angrychisel/makelab-chs-MCAPP/MORGAN/FAB APPROVED STL/STL OUTPUT SETTINGS.PNG

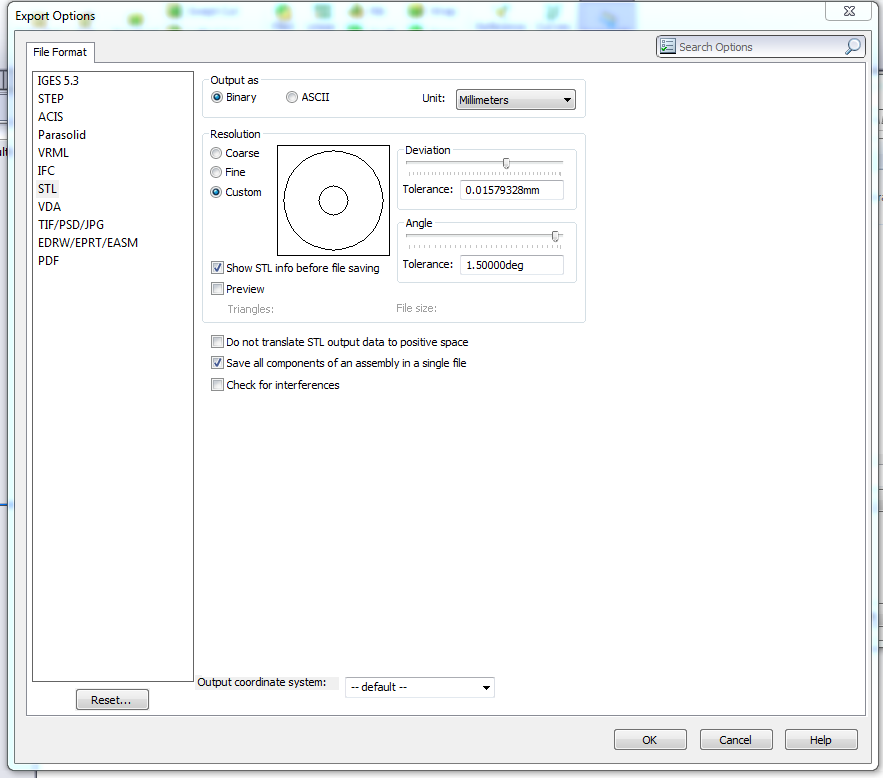
MORGAN/FAB APPROVED STL/STL OUTPUT SETTINGS.PNG
