angrychisel/makelab-chs-MCAPP/MORGAN/IMAGES/2013-07-30 22.37.16.jpg

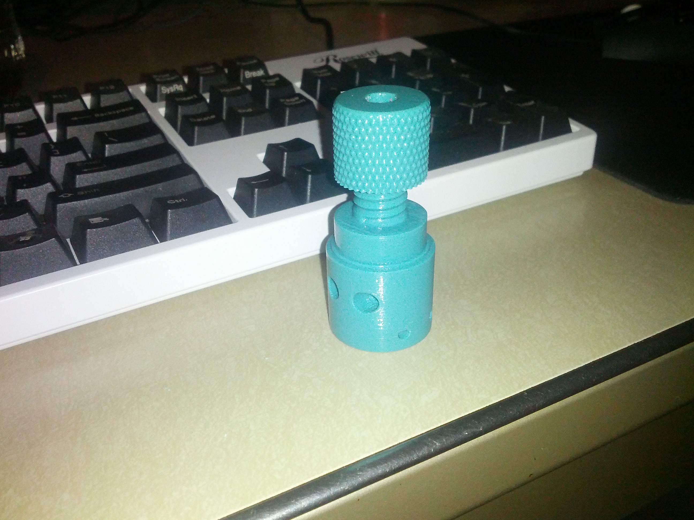
MORGAN/IMAGES/2013-07-30 22.37.16.jpg
