angrychisel/makelab-chs-MCAPP/MORGAN/IMAGES/2013-07-30 22.37.23.jpg

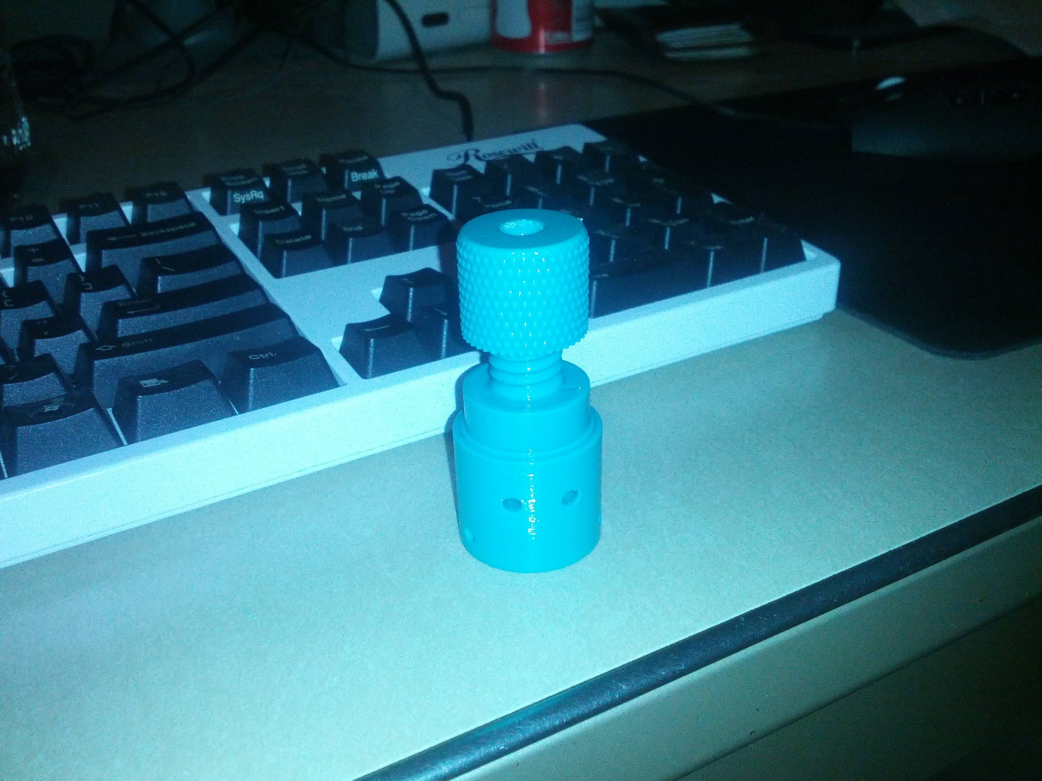
MORGAN/IMAGES/2013-07-30 22.37.23.jpg
