angrychisel/makelab-chs-MCAPP/MORGAN/IMAGES/2013-07-30 22.37.25.jpg

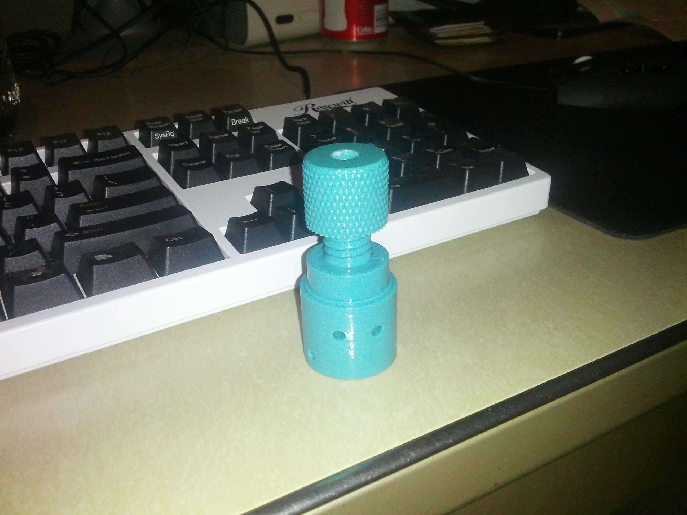
MORGAN/IMAGES/2013-07-30 22.37.25.jpg
