angrychisel/makelab-chs-MCAPP/MORGAN/IMAGES/2013-07-30 22.37.32.jpg

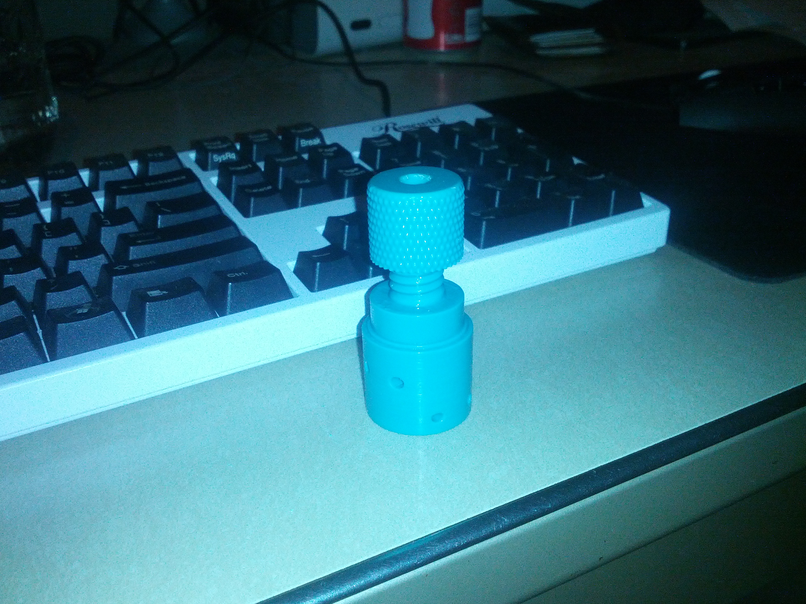
MORGAN/IMAGES/2013-07-30 22.37.32.jpg
