angrychisel/makelab-chs-MCAPP/MORGAN/IMAGES/2013-07-30 22.38.56.jpg

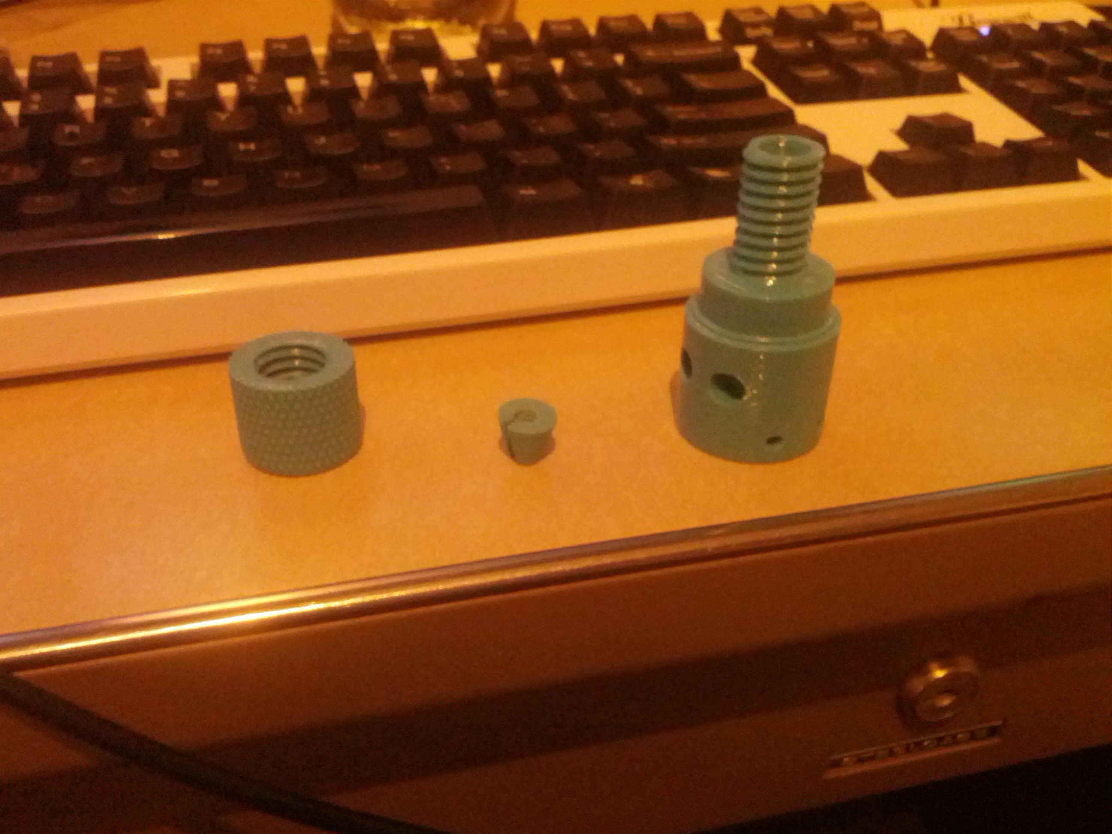
MORGAN/IMAGES/2013-07-30 22.38.56.jpg
