angrychisel/makelab-chs-MCAPP/MORGAN/IMAGES/2013-07-30 22.39.08.jpg

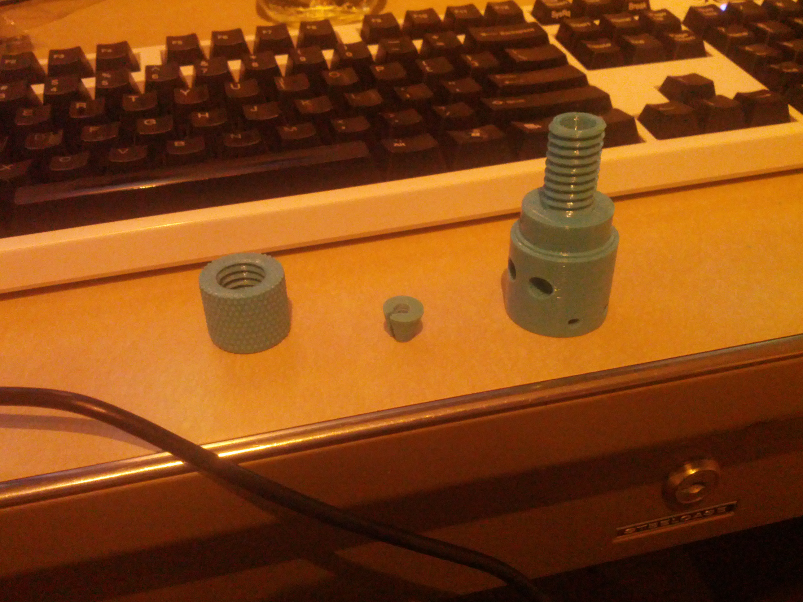
MORGAN/IMAGES/2013-07-30 22.39.08.jpg
