angrychisel/makelab-chs-MCAPP/MORGAN/IMAGES/2013-07-31 16.57.55.jpg

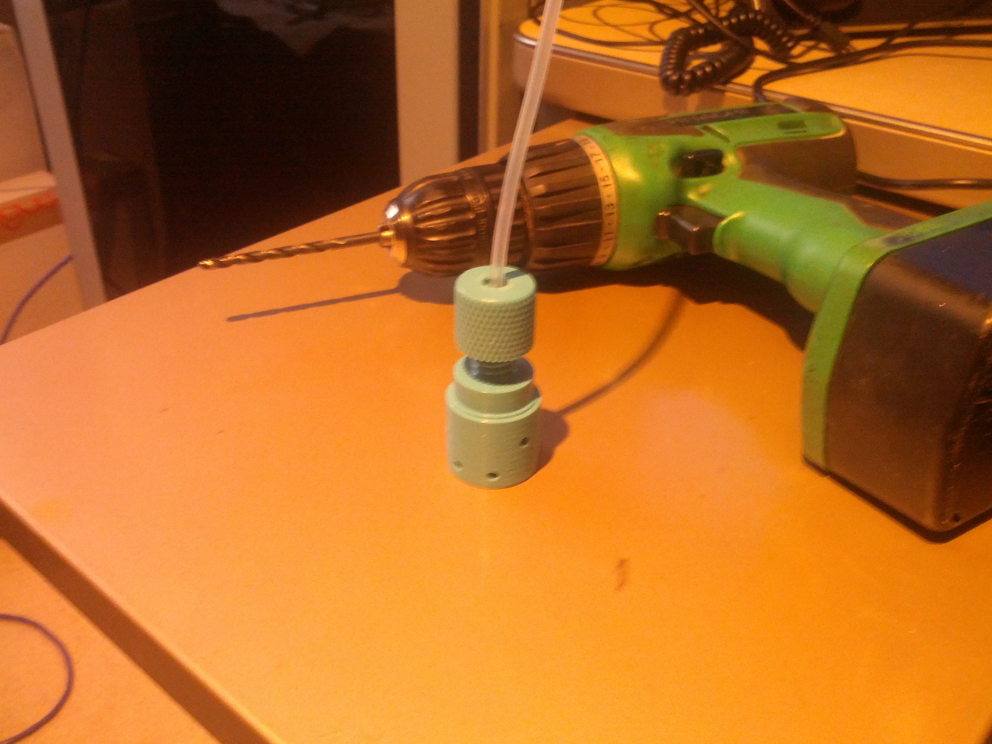
MORGAN/IMAGES/2013-07-31 16.57.55.jpg
