angrychisel/makelab-chs-MCAPP/MORGAN/IMAGES/2013-07-31 16.58.13.jpg

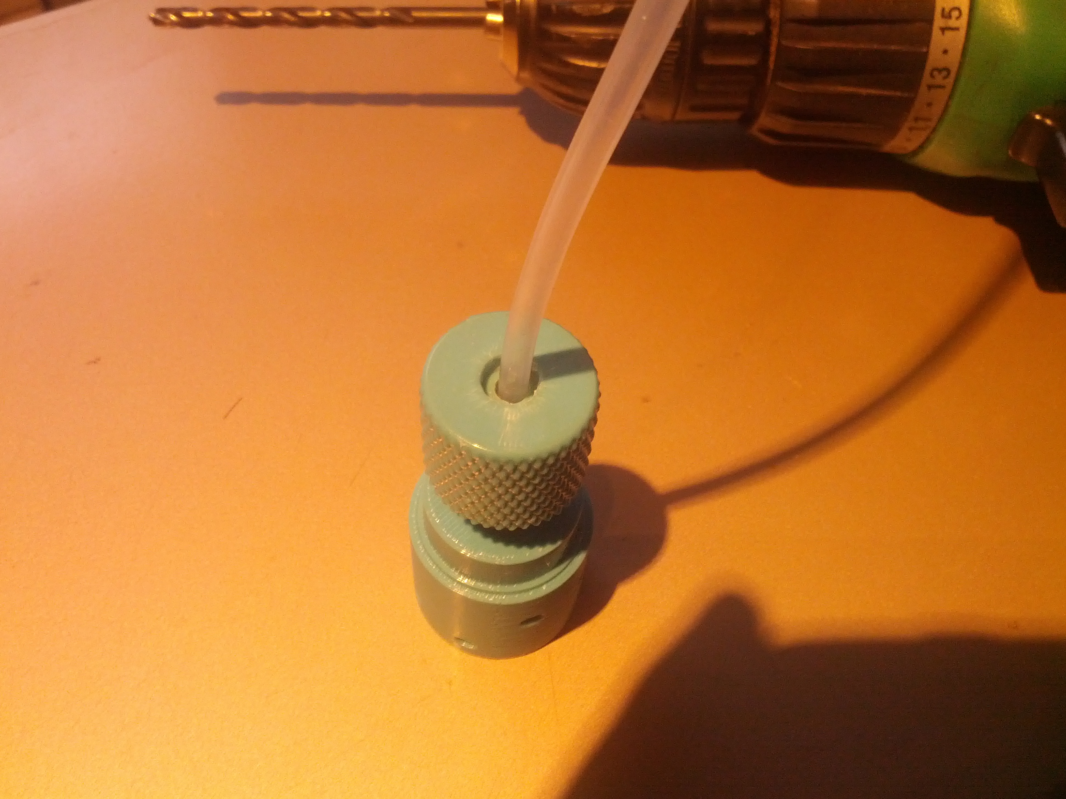
MORGAN/IMAGES/2013-07-31 16.58.13.jpg
