angrychisel/makelab-chs-MCAPP/MORGAN/IMAGES/2013-07-31 16.58.45.jpg

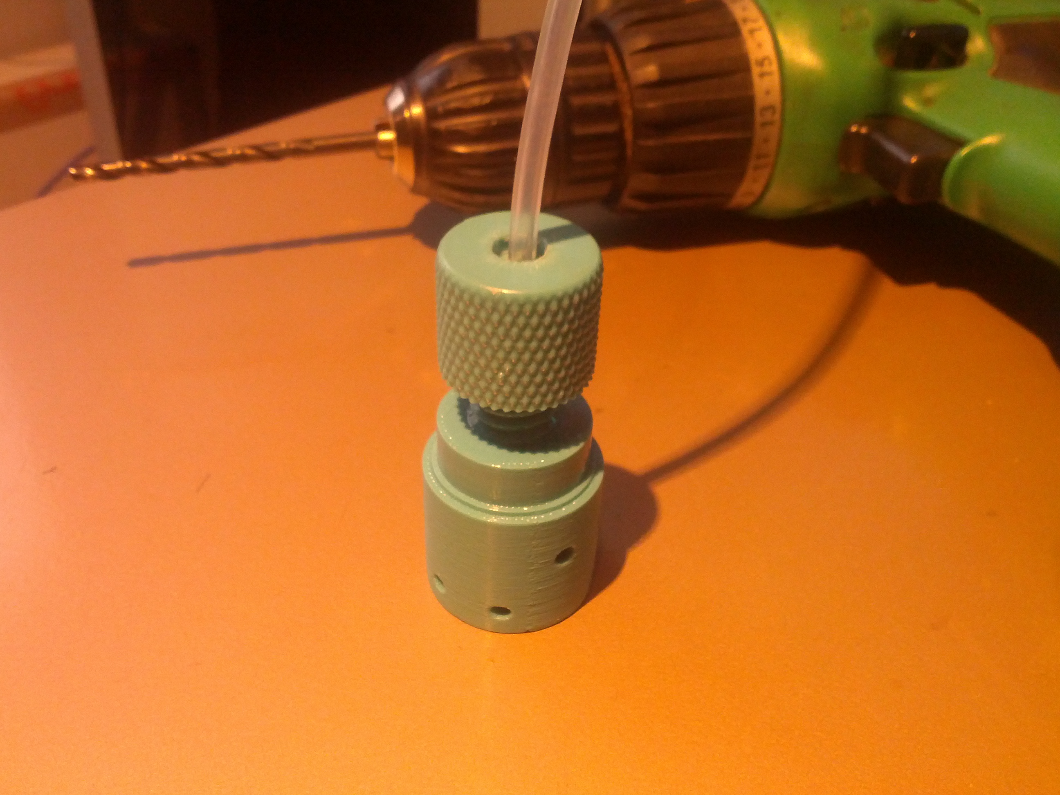
MORGAN/IMAGES/2013-07-31 16.58.45.jpg
