angrychisel/makelab-chs-MCAPP/MORGAN/IMAGES/2013-07-31 17.22.50.jpg

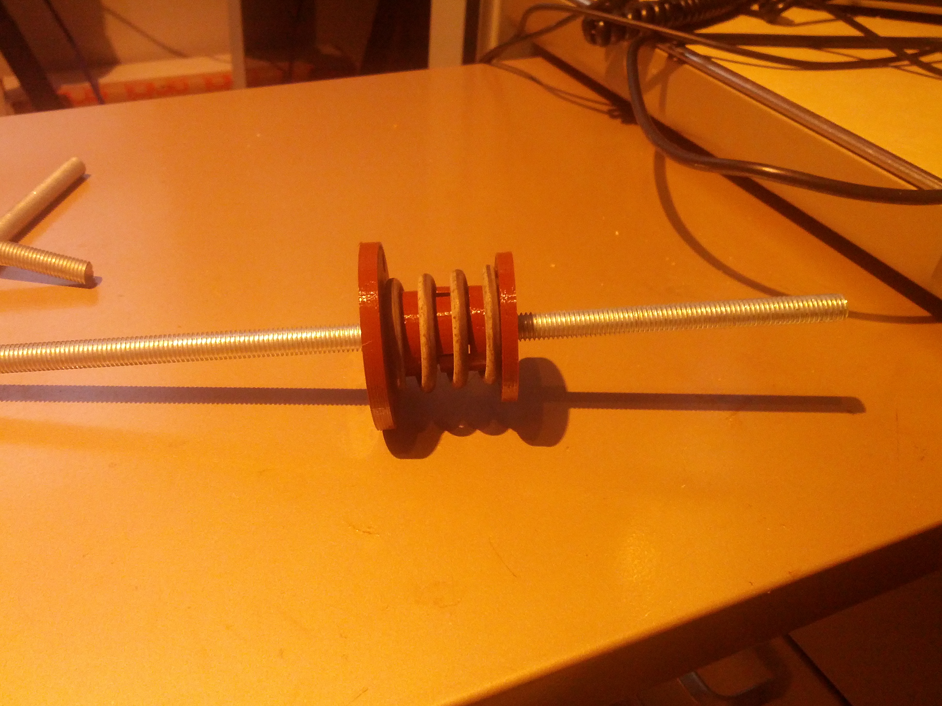
MORGAN/IMAGES/2013-07-31 17.22.50.jpg
