angrychisel/makelab-chs-MCAPP/MORGAN/IMAGES/2013-07-31 17.23.13.jpg

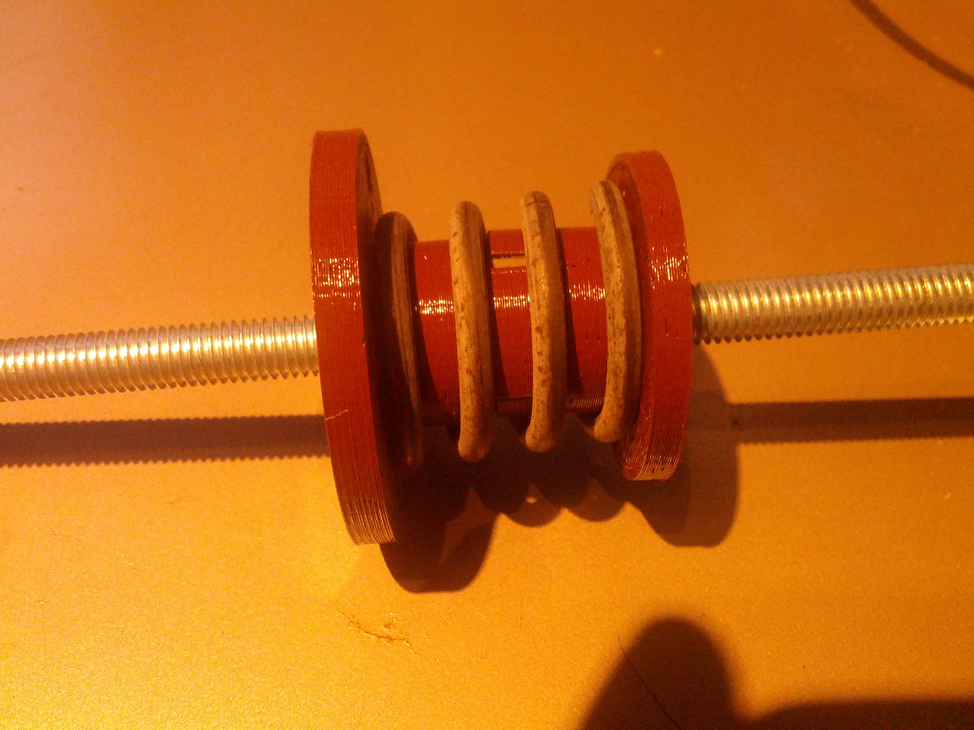
MORGAN/IMAGES/2013-07-31 17.23.13.jpg
