angrychisel/makelab-chs-MCAPP/MORGAN/IMAGES/2013-08-02 20.06.50.jpg

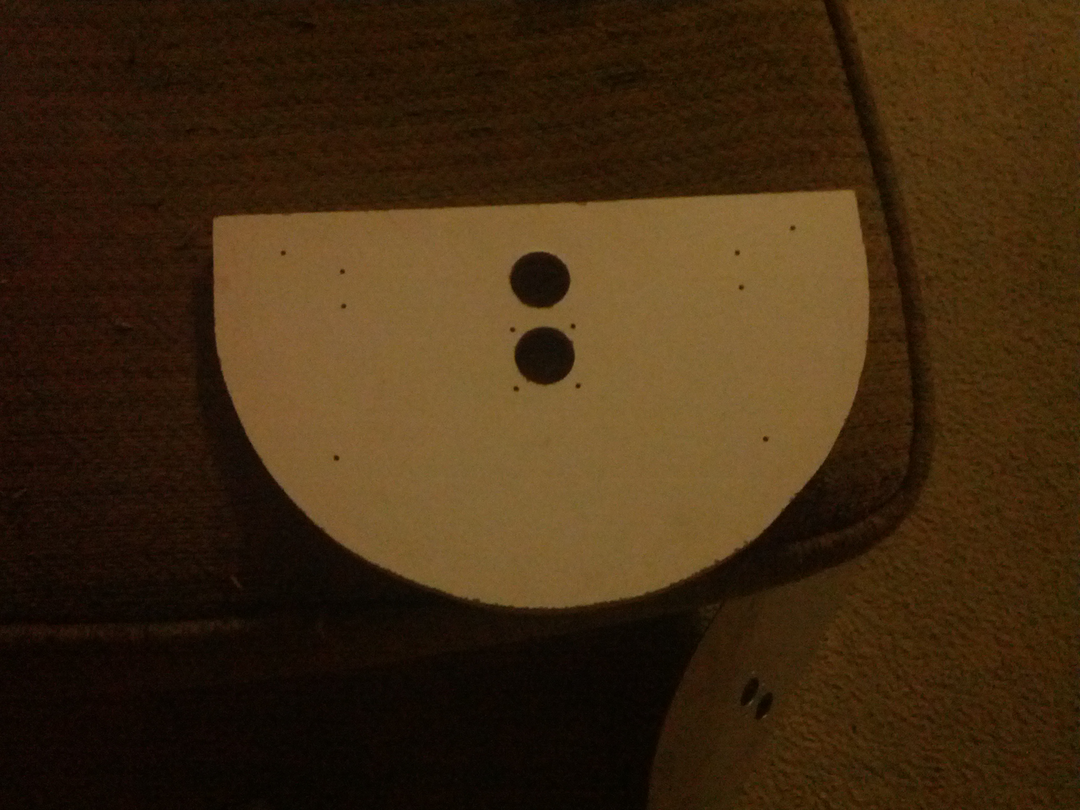
MORGAN/IMAGES/2013-08-02 20.06.50.jpg
