angrychisel/makelab-chs-MCAPP/MORGAN/IMAGES/2013-08-02 20.07.16.jpg

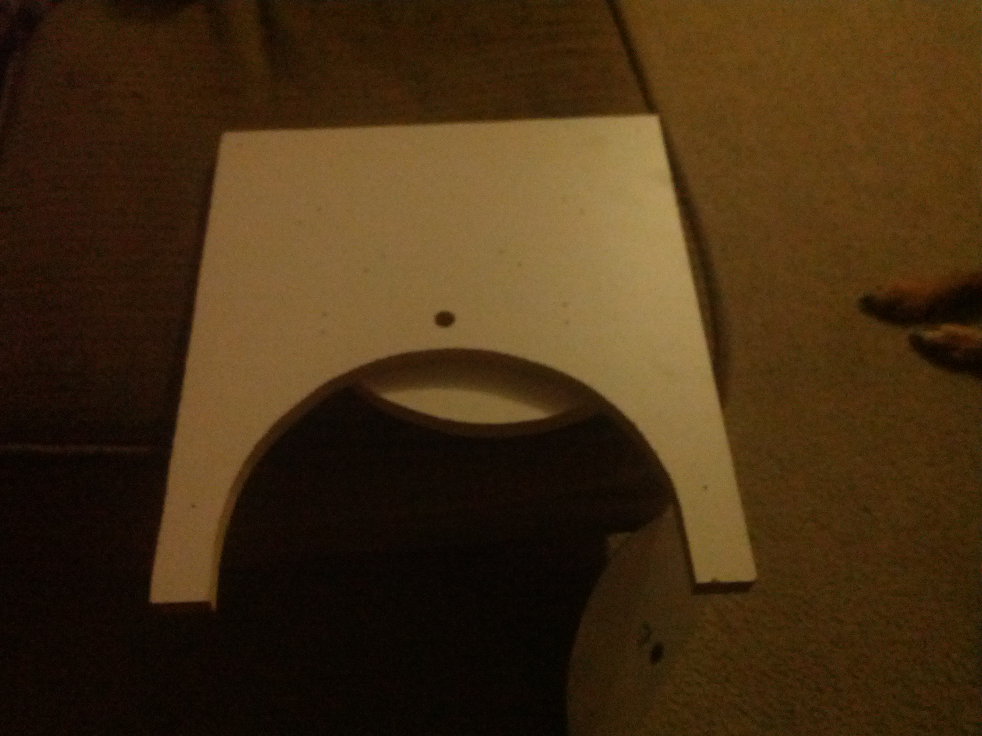
MORGAN/IMAGES/2013-08-02 20.07.16.jpg
