angrychisel/makelab-chs-MCAPP/MORGAN/IMAGES/2013-08-03 15.07.32.jpg

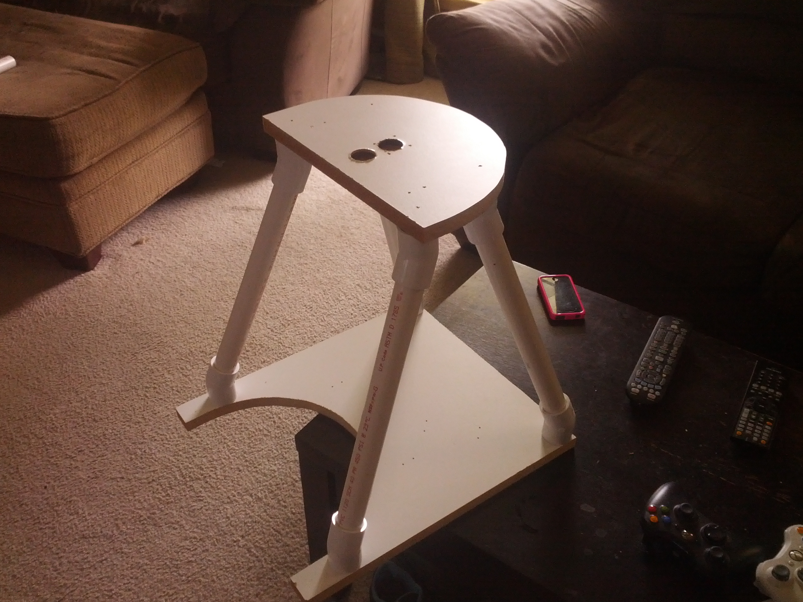
MORGAN/IMAGES/2013-08-03 15.07.32.jpg
