angrychisel/makelab-chs-MCAPP/MORGAN/IMAGES/image005.jpg

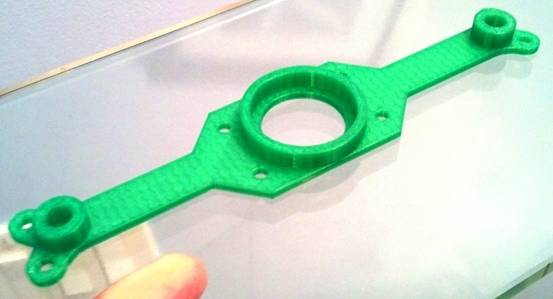
MORGAN/IMAGES/image005.jpg
