angrychisel/makelab-chs-MCAPP/MORGAN/IMAGES/image006.jpg

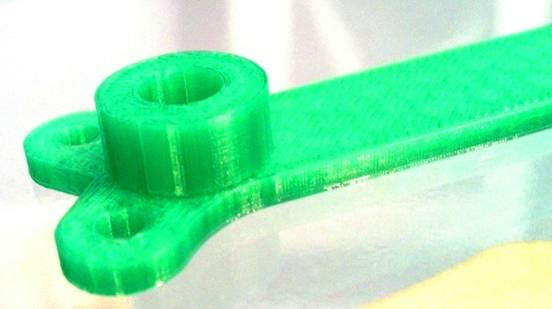
MORGAN/IMAGES/image006.jpg
