angrychisel/makelab-chs-MCAPP/MORGAN/Morgan-master/MorganHarley1.jpg

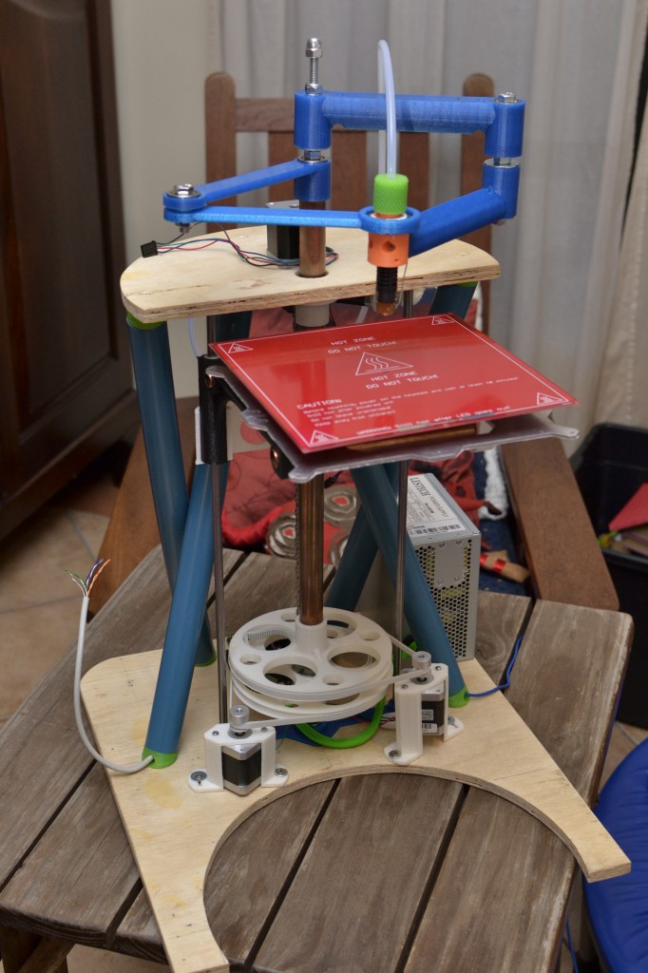
MORGAN/Morgan-master/MorganHarley1.jpg
