angrychisel/makelab-chs-MCAPP/MORGAN/FAB APPROVED STL/MLC-1-0029.STL

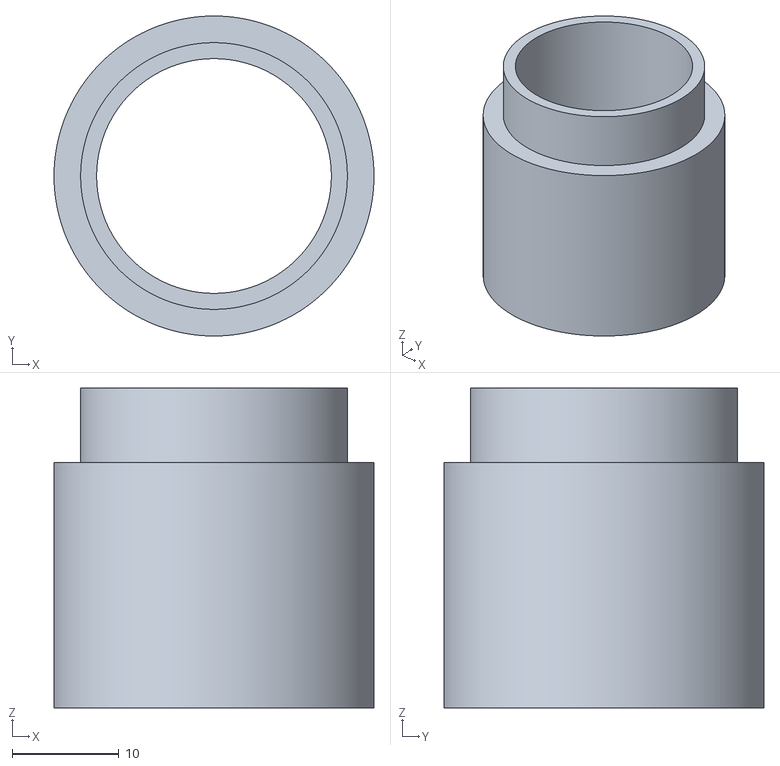
[picture p51: CAD file, 2013-08-08]
MORGAN/FAB APPROVED STL/MLC-1-0029.STL
30.0 x 30.0 x 30.0
