angrychisel/makelab-chs-MCAPP/MORGAN/Morgan-master/dxf/UNIVERSAL PLATE.SLDPRT

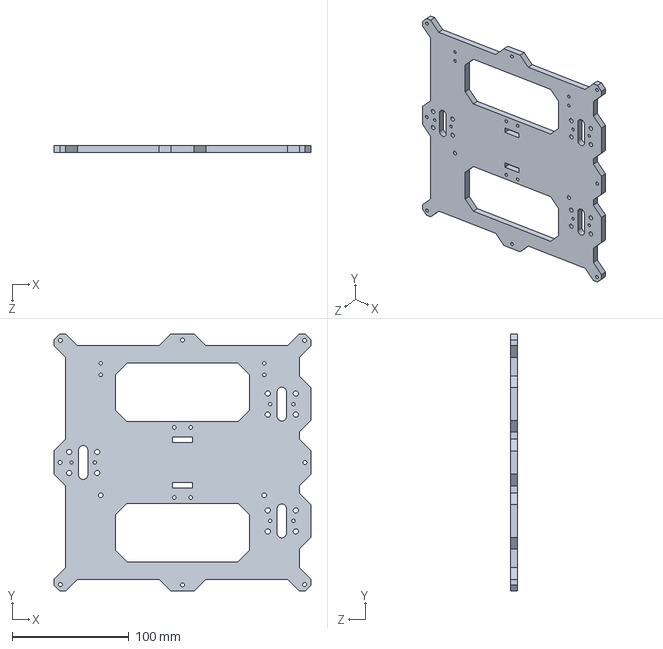
[picture p52: CAD file, 2013-07-29]
MORGAN/Morgan-master/dxf/UNIVERSAL PLATE.SLDPRT
220.0 x 220.0 x 6.35 mm
