angrychisel/makelab-chs-MCAPP/MORGAN/Morgan-master/source/Base_and_Riser_2.stl

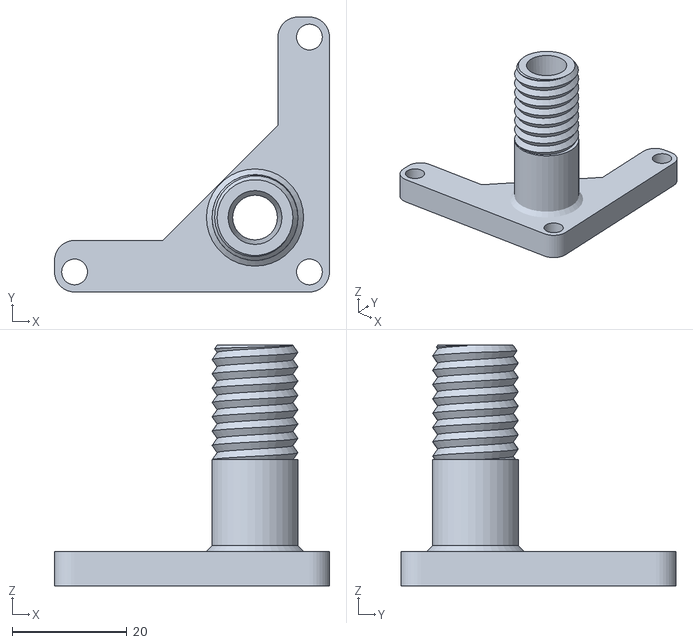
[picture p53: CAD file, 2013-07-25]
MORGAN/Morgan-master/source/Base_and_Riser_2.stl
48.0 x 48.0 x 42.0
