angrychisel/makelab-chs-MCAPP/MORGAN/Morgan-master/stl/NEMA17STEPPER.SLDPRT

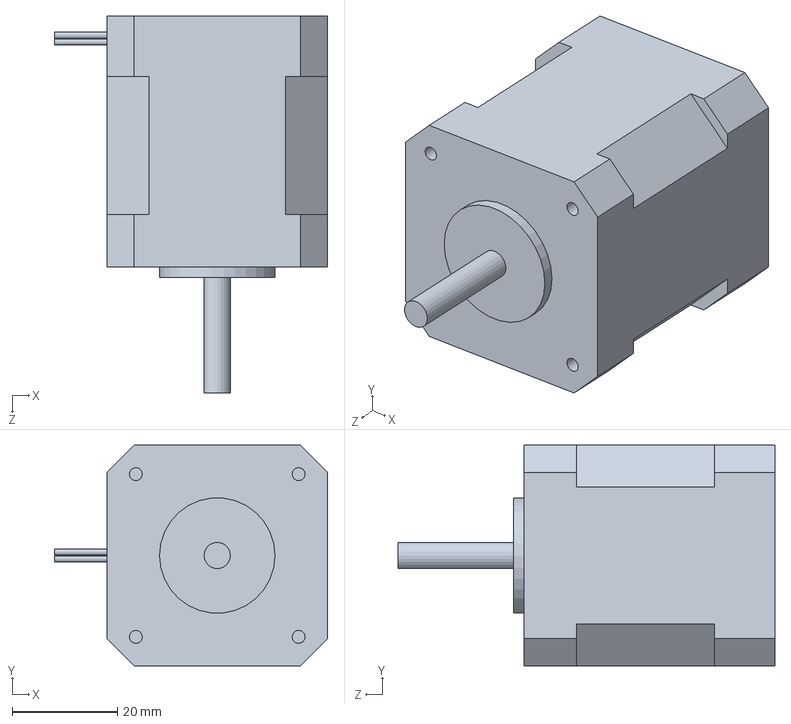
[picture p54: CAD file, 2013-07-26]
MORGAN/Morgan-master/stl/NEMA17STEPPER.SLDPRT
52.0 x 42.0 x 71.8 mm
