angrychisel/makelab-chs-MCAPP/MORGAN/WORM EXTRUDER/g1034.SLDPRT

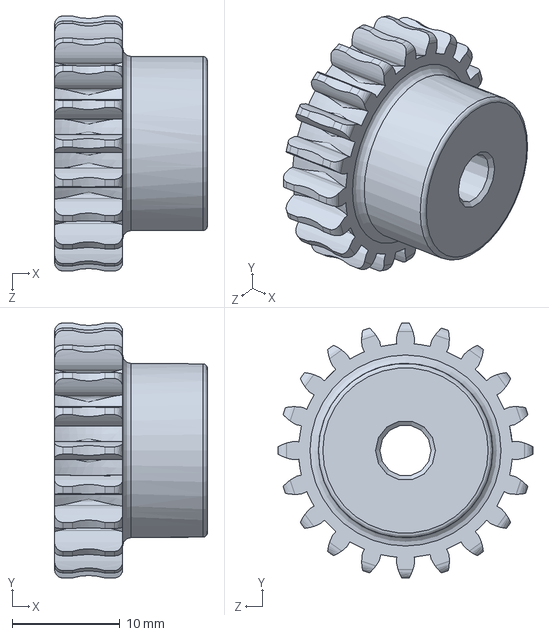
[picture p55: CAD file, 2013-07-27]
MORGAN/WORM EXTRUDER/g1034.SLDPRT
14.2 x 23.7 x 23.7 mm
