angrychisel/makelab-chs-MCAPP/MORGAN/ACCESSORIES/SPOOL ROLLER.SLDPRT

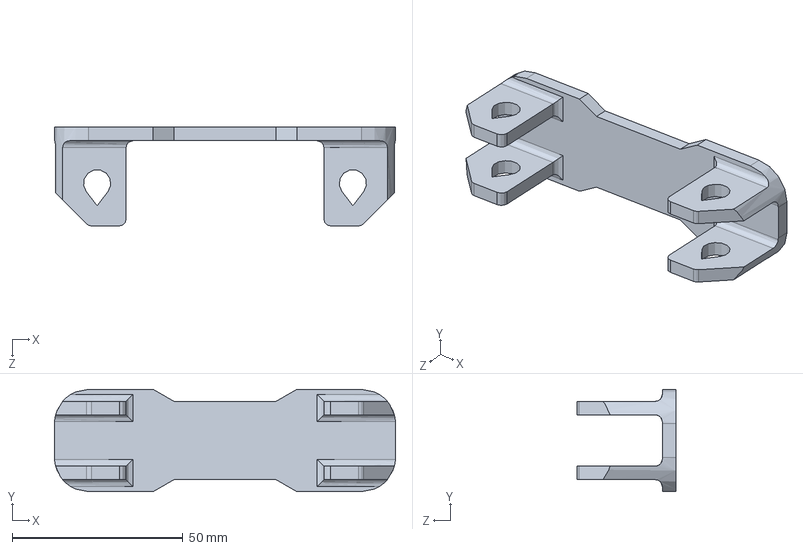
[picture p56: CAD file, 2013-10-28]
MORGAN/ACCESSORIES/SPOOL ROLLER.SLDPRT
100.0 x 30.0 x 29.0 mm
