angrychisel/makelab-chs-MCAPP/MORGAN/FAB APPROVED STL/MLC-1-0019.STL

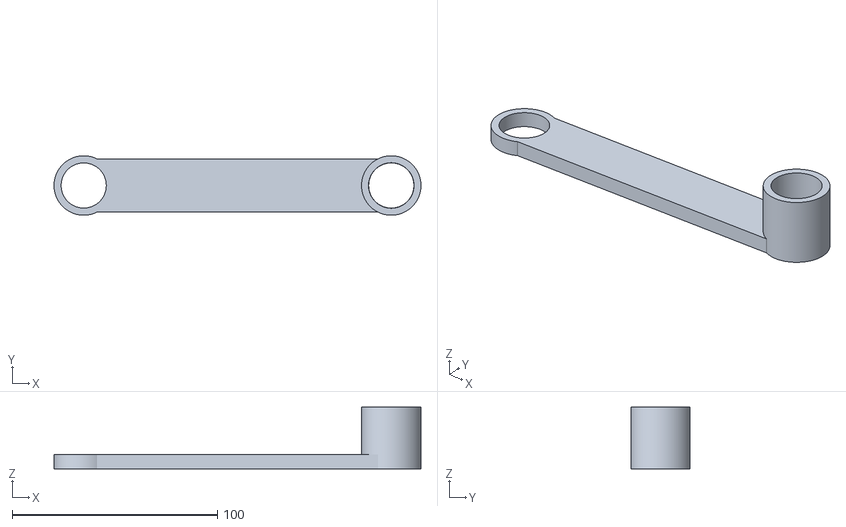
[picture p57: CAD file, 2013-08-04]
MORGAN/FAB APPROVED STL/MLC-1-0019.STL
179.0 x 29.0 x 30.0
