angrychisel/makelab-chs-MCAPP/MORGAN/good extruder/h3216.SLDPRT

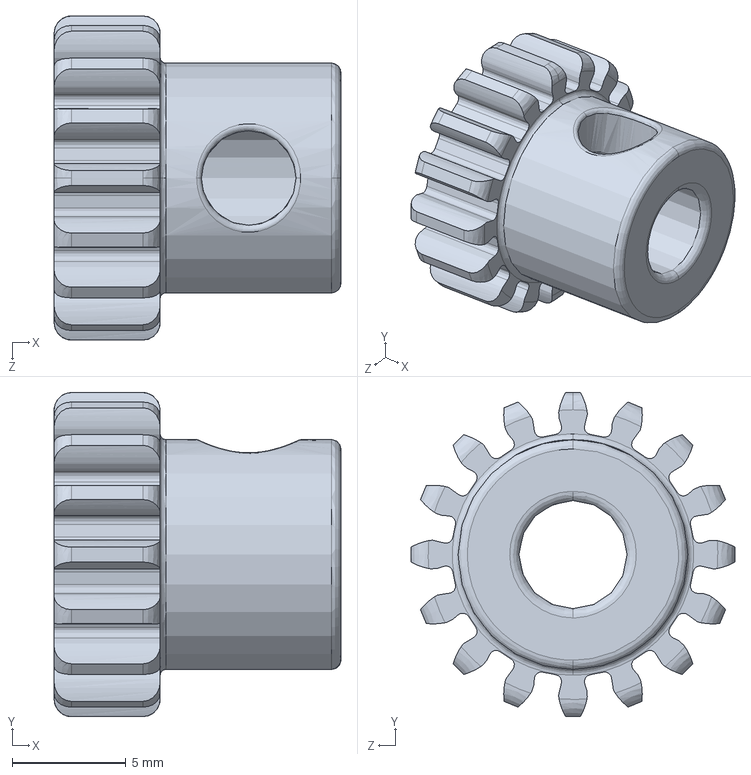
[picture p58: CAD file, 2013-09-19]
MORGAN/good extruder/h3216.SLDPRT
12.6 x 14.3 x 14.3 mm
