angrychisel/makelab-chs-MCAPP/MORGAN/MLC-1-0017.SLDPRT

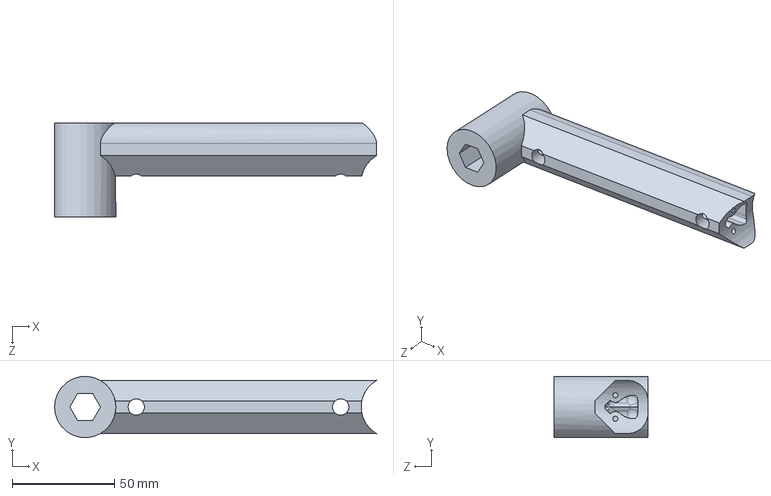
[picture p59: CAD file, 2013-10-12]
MORGAN/MLC-1-0017.SLDPRT
157.5 x 29.9 x 46.0 mm
