angrychisel/makelab-chs-MCAPP/MORGAN/Morgan-master/dxf/OpenHW_Universal-XPlate.dxf

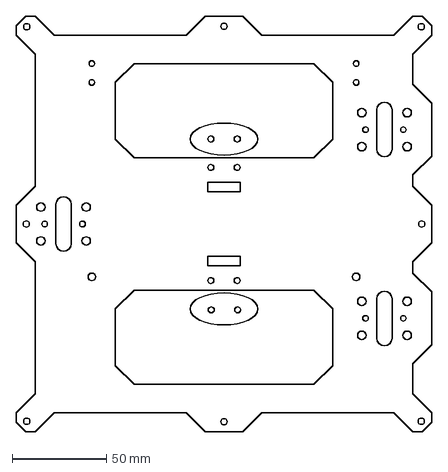
[picture p60: CAD file, 2013-07-25]
MORGAN/Morgan-master/dxf/OpenHW_Universal-XPlate.dxf
220.0 x 220.0 mm
