angrychisel/makelab-chs-MCAPP/MORGAN/Morgan-master/stl/19-Morgan_arm_Theta_a.stl

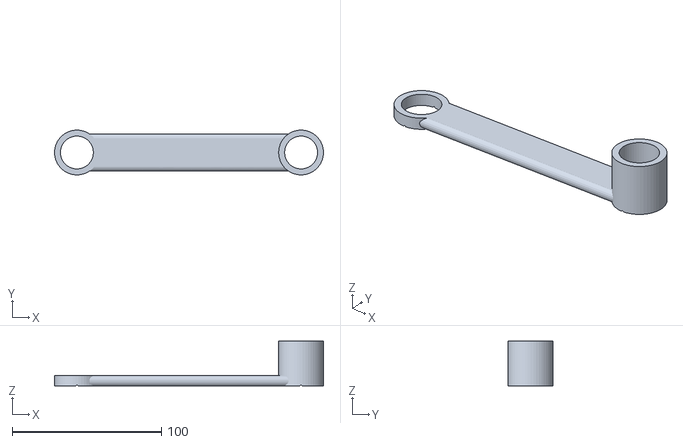
[picture p61: CAD file, 2013-07-25]
MORGAN/Morgan-master/stl/19-Morgan_arm_Theta_a.stl
180.0 x 29.9 x 30.0
