angrychisel/makelab-chs-MCAPP/MORGAN/WORM EXTRUDER/g1035.SLDPRT

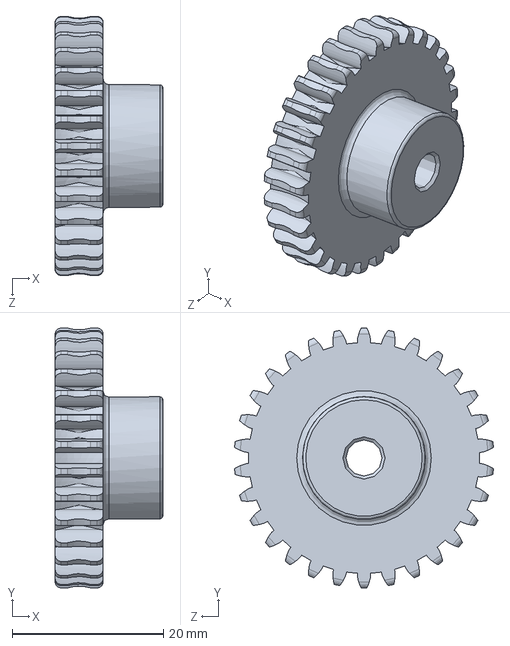
[picture p62: CAD file, 2013-07-27]
MORGAN/WORM EXTRUDER/g1035.SLDPRT
14.2 x 34.3 x 34.2 mm
