angrychisel/makelab-chs-MCAPP/MORGAN/EXPERIMENTAL/testcube.SLDPRT

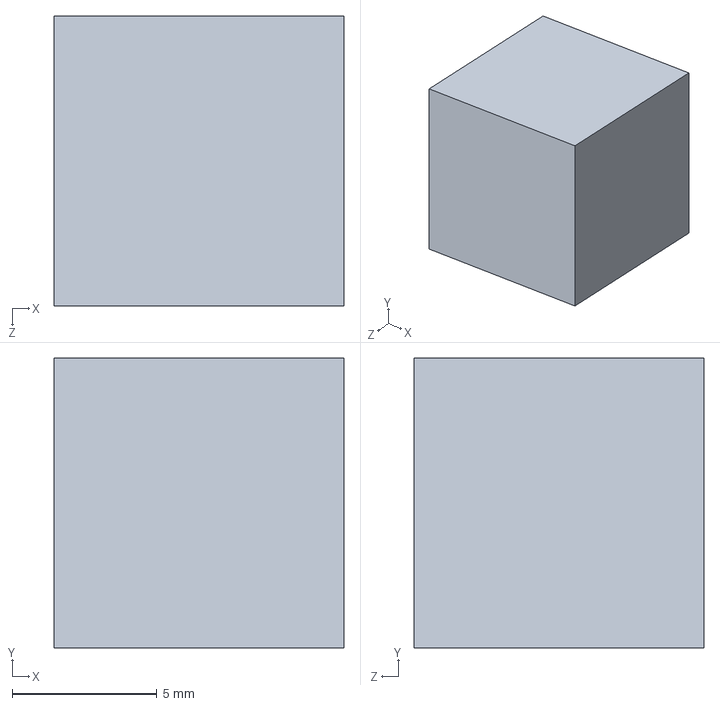
[picture p63: CAD file, 2013-09-19]
MORGAN/EXPERIMENTAL/testcube.SLDPRT
10.0 x 10.0 x 10.0 mm
