angrychisel/makelab-chs-MCAPP/MORGAN/FAB APPROVED STL/MLC-1-002.DXF

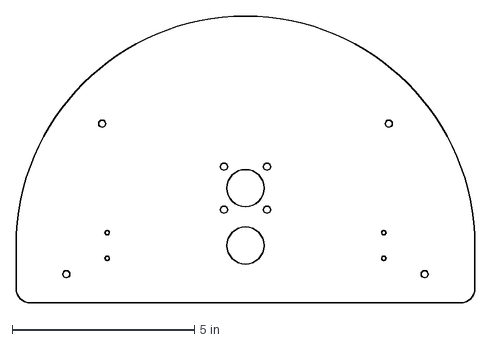
[picture p64: CAD file, 2013-08-02]
MORGAN/FAB APPROVED STL/MLC-1-002.DXF
12.6 x 7.87 in
