angrychisel/makelab-chs-MCAPP/MORGAN/good extruder/spur gear_ai.sldprt

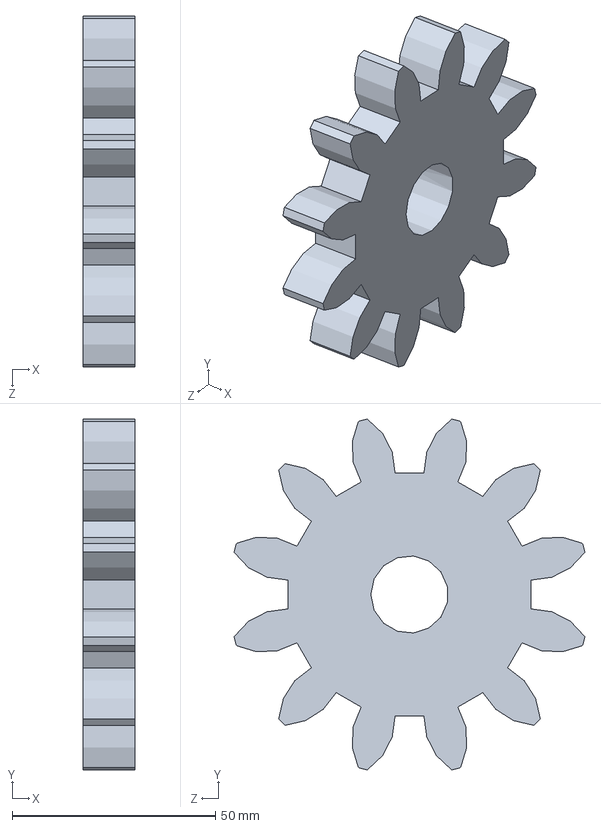
[picture p65: CAD file, 2013-09-19]
MORGAN/good extruder/spur gear_ai.sldprt
12.7 x 86.4 x 86.4 mm
