angrychisel/makelab-chs-MCAPP/MORGAN/Morgan-master/dxf/platform_cutting.dxf

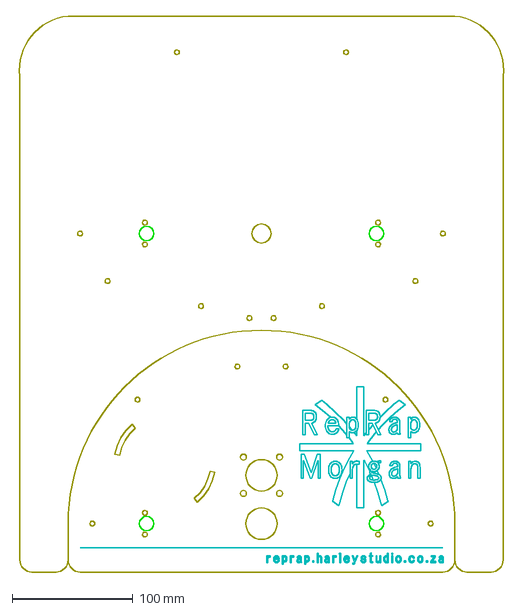
[picture p66: CAD file, 2013-07-25]
MORGAN/Morgan-master/dxf/platform_cutting.dxf
405.5 x 460.0 mm
