angrychisel/makelab-chs-MCAPP/MORGAN/Morgan-master/stl/01-pvc_pipe_support_a.SLDPRT

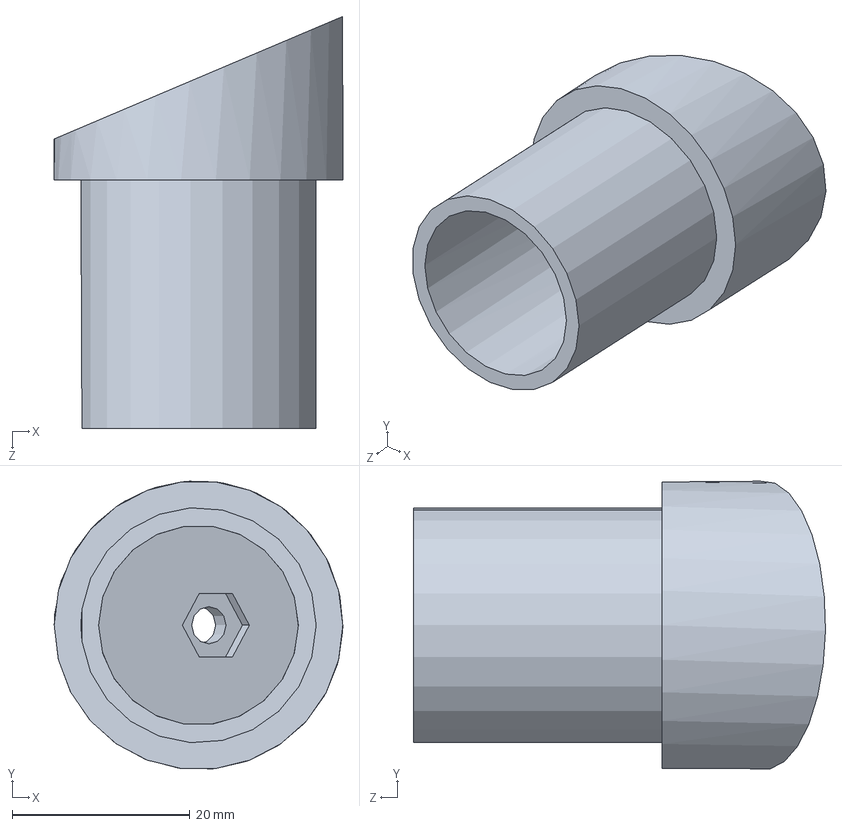
[picture p67: CAD file, 2013-07-25]
MORGAN/Morgan-master/stl/01-pvc_pipe_support_a.SLDPRT
32.5 x 32.4 x 46.4 mm
