angrychisel/makelab-chs-MCAPP/MORGAN/WORM EXTRUDER/LUHB.SLDPRT

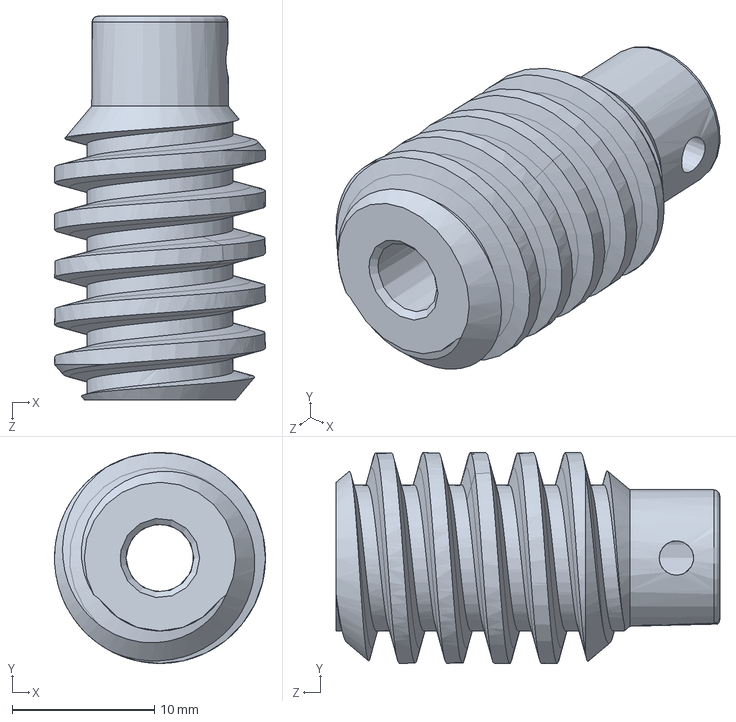
[picture p68: CAD file, 2013-07-27]
MORGAN/WORM EXTRUDER/LUHB.SLDPRT
14.8 x 14.8 x 26.9 mm
