angrychisel/makelab-chs-MCAPP/MORGAN/EXPERIMENTAL/HEATBED BASE PLATE.SLDPRT

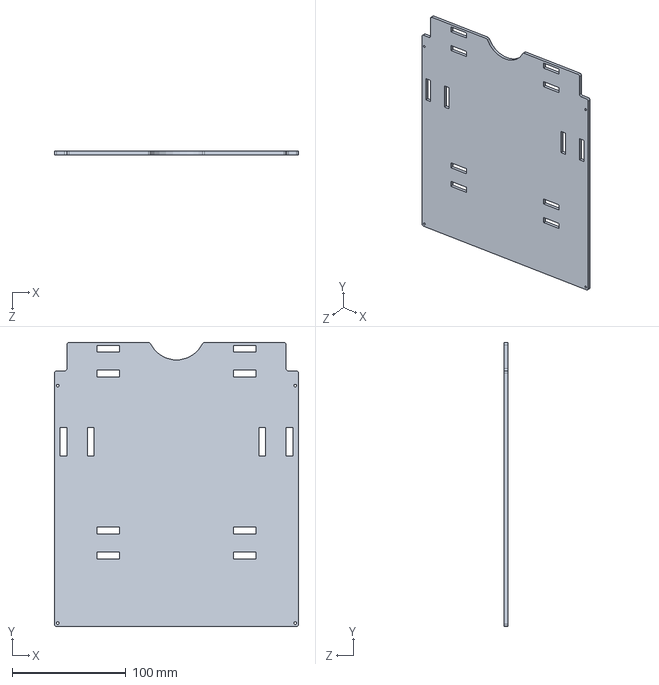
[picture p69: CAD file, 2013-09-14]
MORGAN/EXPERIMENTAL/HEATBED BASE PLATE.SLDPRT
215.0 x 250.0 x 3.17 mm
