angrychisel/makelab-chs-MCAPP/MORGAN/FAB APPROVED STL/MLC-1-001.DXF

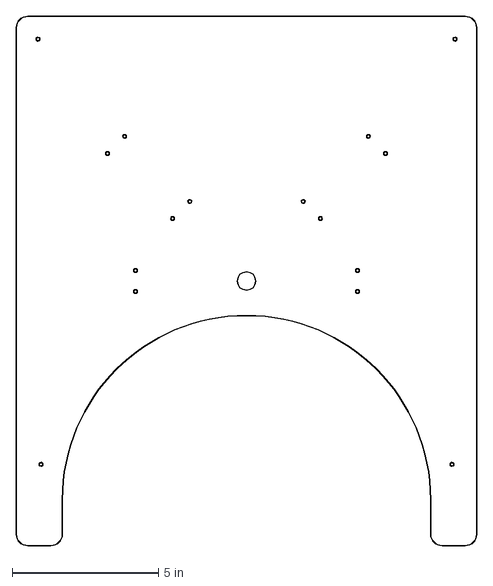
[picture p70: CAD file, 2013-08-02]
MORGAN/FAB APPROVED STL/MLC-1-001.DXF
15.7 x 18.1 in
