angrychisel/makelab-chs-MCAPP/MORGAN/MK2A Heatbed.SLDPRT

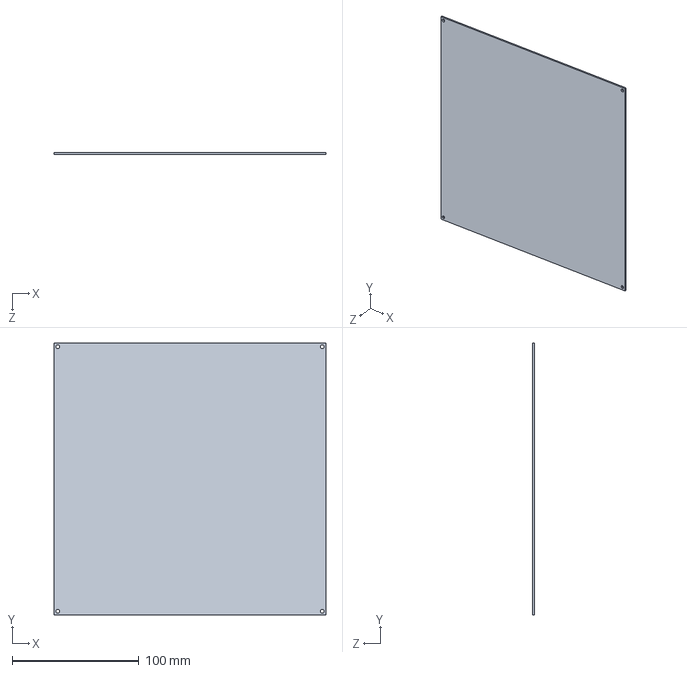
[picture p71: CAD file, 2013-09-10]
MORGAN/MK2A Heatbed.SLDPRT
215.0 x 215.0 x 1.60 mm
