angrychisel/makelab-chs-MCAPP/MORGAN/Morgan-master/stl/cap_2.stl

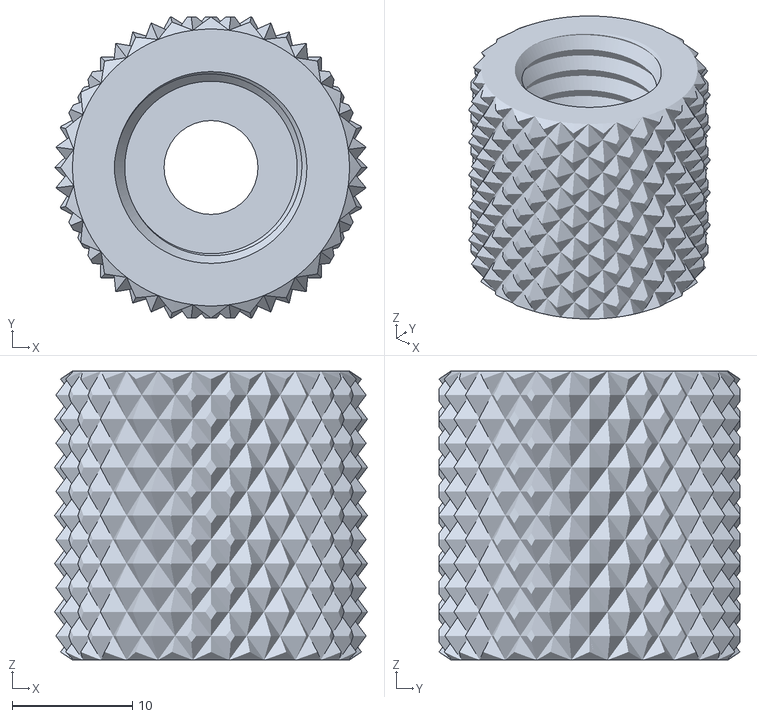
[picture p72: CAD file, 2013-07-25]
MORGAN/Morgan-master/stl/cap_2.stl
26.0 x 25.0 x 24.0
