angrychisel/makelab-chs-MCAPP/MORGAN/WORM EXTRUDER/STEPPER BASE.SLDPRT

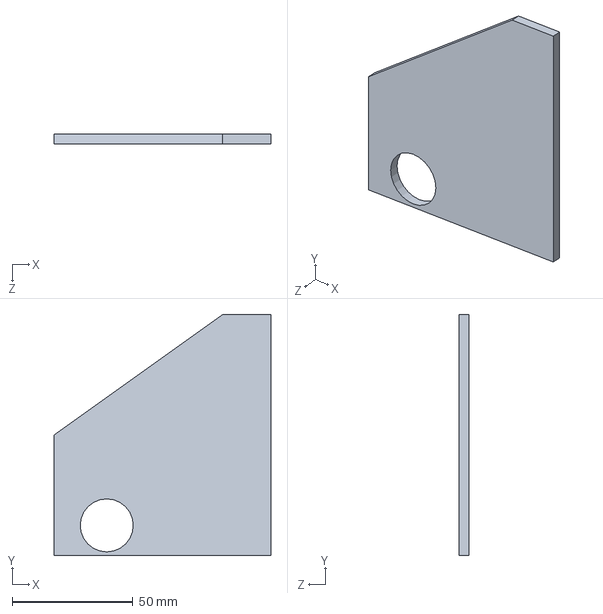
[picture p73: CAD file, 2013-07-27]
MORGAN/WORM EXTRUDER/STEPPER BASE.SLDPRT
90.0 x 100.0 x 4.00 mm
