angrychisel/makelab-chs-MCAPP/MORGAN/FAB APPROVED STL/MLC-1-0020.STL

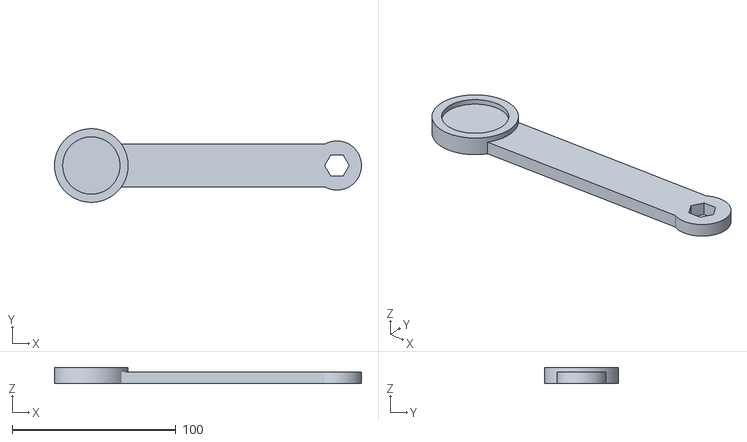
[picture p74: CAD file, 2013-08-01]
MORGAN/FAB APPROVED STL/MLC-1-0020.STL
187.5 x 45.0 x 10.00
