angrychisel/makelab-chs-MCAPP/MORGAN/MLC-1-009.SLDPRT

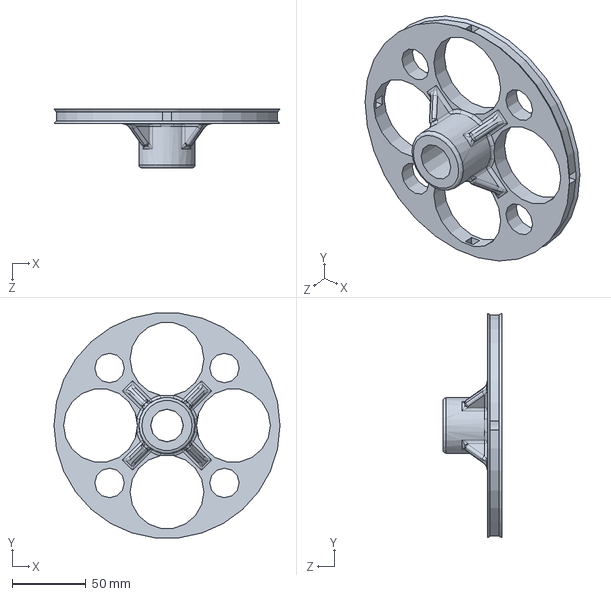
[picture p75: CAD file, 2013-08-04]
MORGAN/MLC-1-009.SLDPRT
153.0 x 152.2 x 40.0 mm
