angrychisel/makelab-chs-MCAPP/MORGAN/Morgan-master/stl/04-z_mount_top_8mm.stl

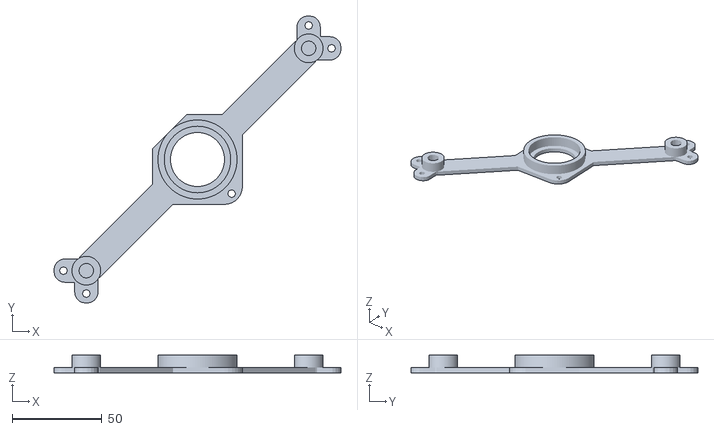
[picture p76: CAD file, 2013-07-25]
MORGAN/Morgan-master/stl/04-z_mount_top_8mm.stl
159.7 x 159.7 x 10.0
