angrychisel/makelab-chs-MCAPP/MORGAN/EXPERIMENTAL/airtripper-extruder-v3.SLDPRT

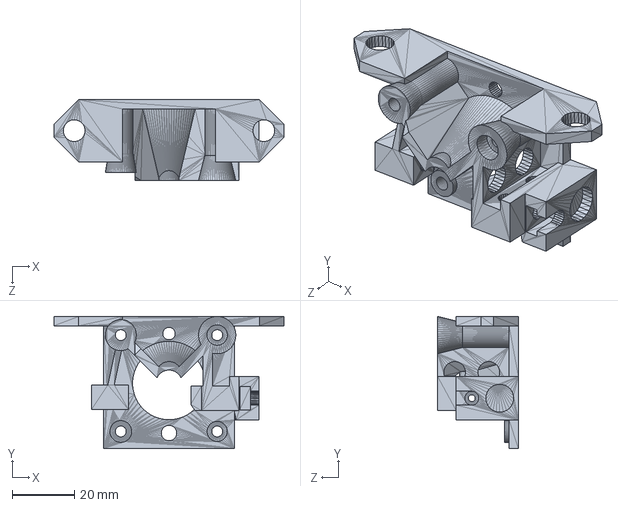
[picture p77: CAD file, 2013-09-13]
MORGAN/EXPERIMENTAL/airtripper-extruder-v3.SLDPRT
74.0 x 42.5 x 26.0 mm
