angrychisel/makelab-chs-MCAPP/MORGAN/FAB APPROVED STL/MLCE-1-002.STL

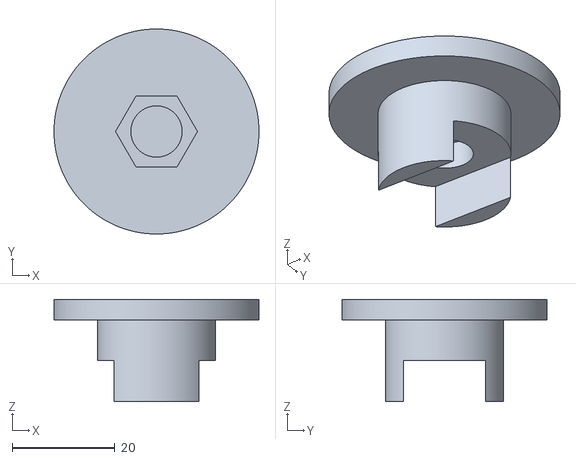
[picture p78: CAD file, 2013-07-30]
MORGAN/FAB APPROVED STL/MLCE-1-002.STL
40.0 x 40.0 x 20.0
