angrychisel/makelab-chs-MCAPP/MORGAN/Morgan-master/stl/23-extruder_bowden_adaptor.stl

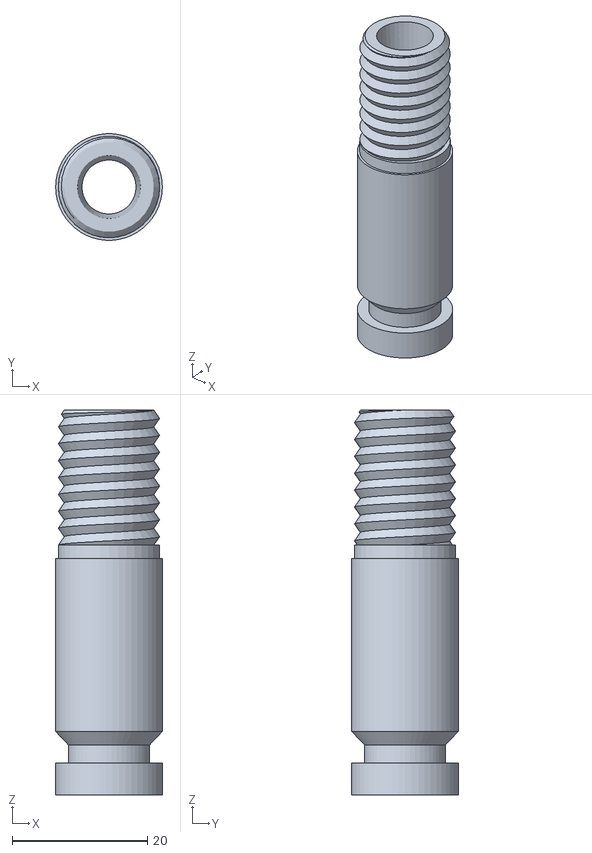
[picture p79: CAD file, 2013-07-25]
MORGAN/Morgan-master/stl/23-extruder_bowden_adaptor.stl
15.8 x 15.8 x 57.0
