angrychisel/makelab-chs-MCAPP/MORGAN/EXPERIMENTAL/50mm riser-short.SLDPRT

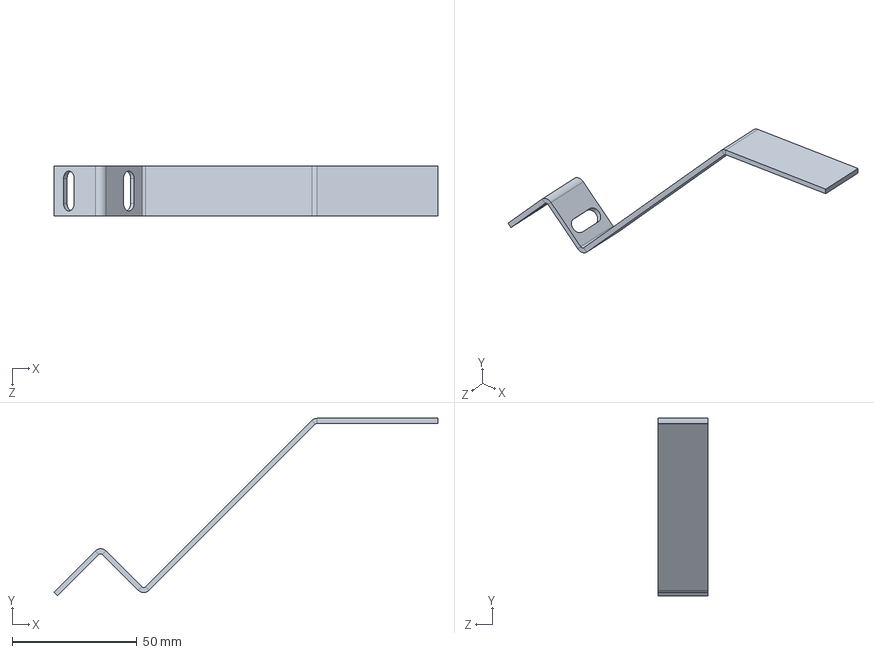
[picture p80: CAD file, 2013-09-10]
MORGAN/EXPERIMENTAL/50mm riser-short.SLDPRT
153.7 x 71.0 x 20.0 mm
