angrychisel/makelab-chs-MCAPP/MORGAN/FAB APPROVED STL/MLCE-1-001.STL

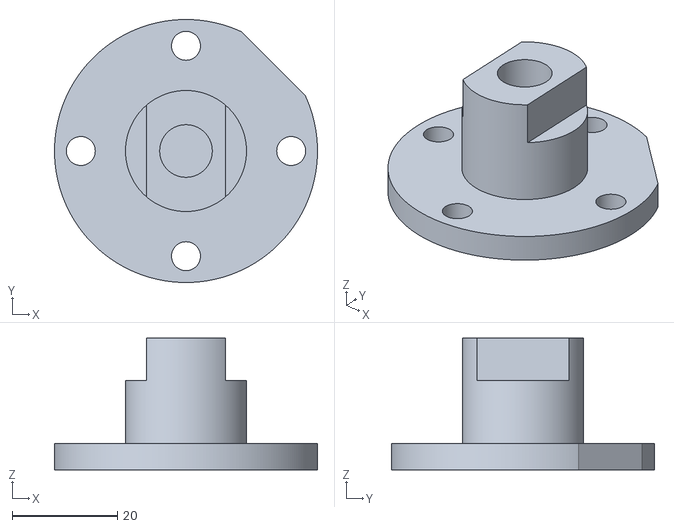
[picture p81: CAD file, 2013-07-30]
MORGAN/FAB APPROVED STL/MLCE-1-001.STL
50.0 x 50.0 x 25.0
