angrychisel/makelab-chs-MCAPP/MORGAN/Morgan-master/stl/24-Morgan_Spool_holder.stl

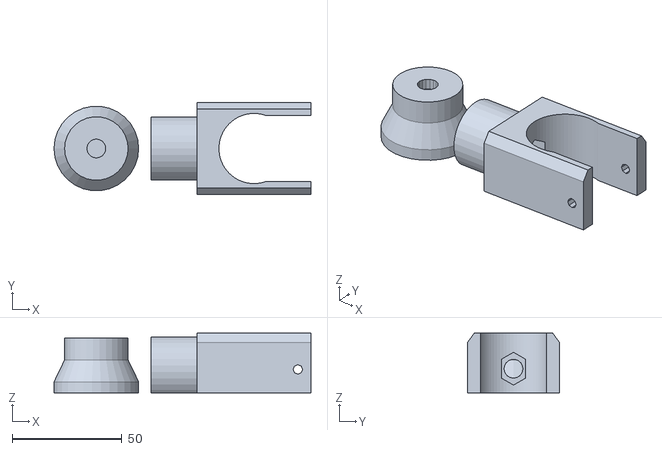
[picture p82: CAD file, 2013-07-25]
MORGAN/Morgan-master/stl/24-Morgan_Spool_holder.stl
117.3 x 42.0 x 27.2
