angrychisel/makelab-chs-MCAPP/MORGAN/EXPERIMENTAL/50mm riser.SLDPRT

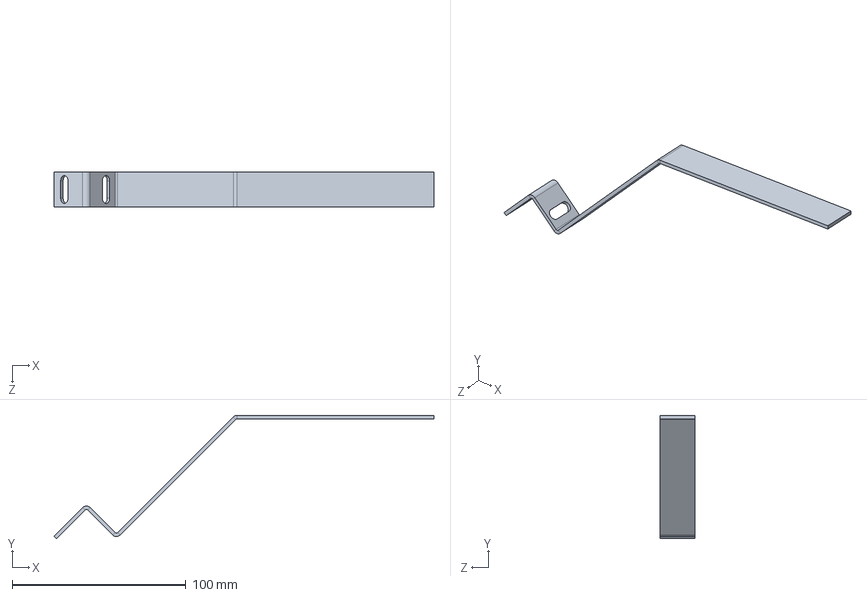
[picture p83: CAD file, 2013-09-10]
MORGAN/EXPERIMENTAL/50mm riser.SLDPRT
218.7 x 71.0 x 20.0 mm
