angrychisel/makelab-chs-MCAPP/MORGAN/FAB APPROVED STL/MLC-1-0018.STL

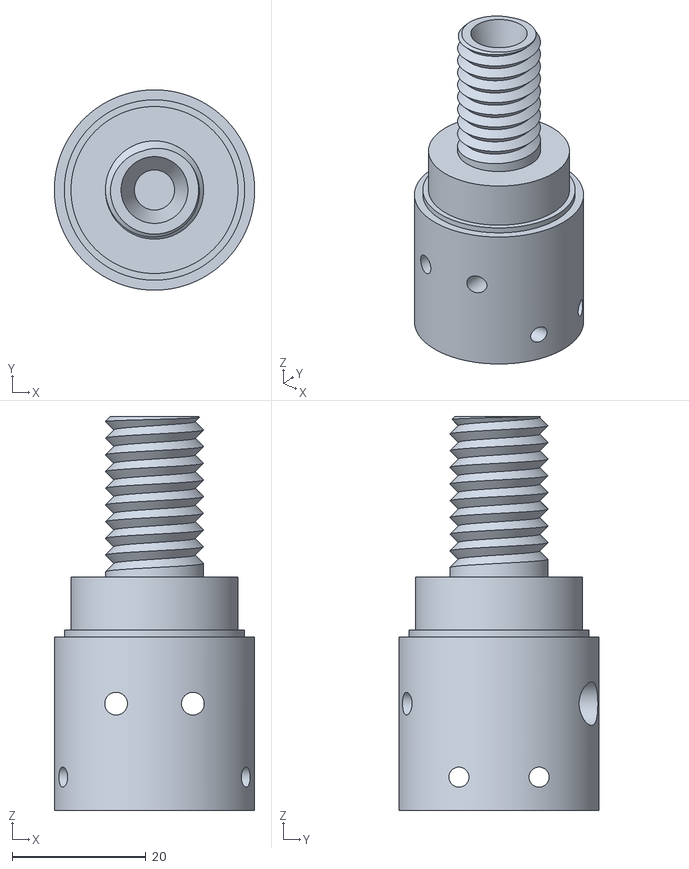
[picture p84: CAD file, 2013-07-30]
MORGAN/FAB APPROVED STL/MLC-1-0018.STL
30.0 x 30.0 x 59.0
