angrychisel/makelab-chs-MCAPP/MORGAN/MLC-1-008.SLDPRT

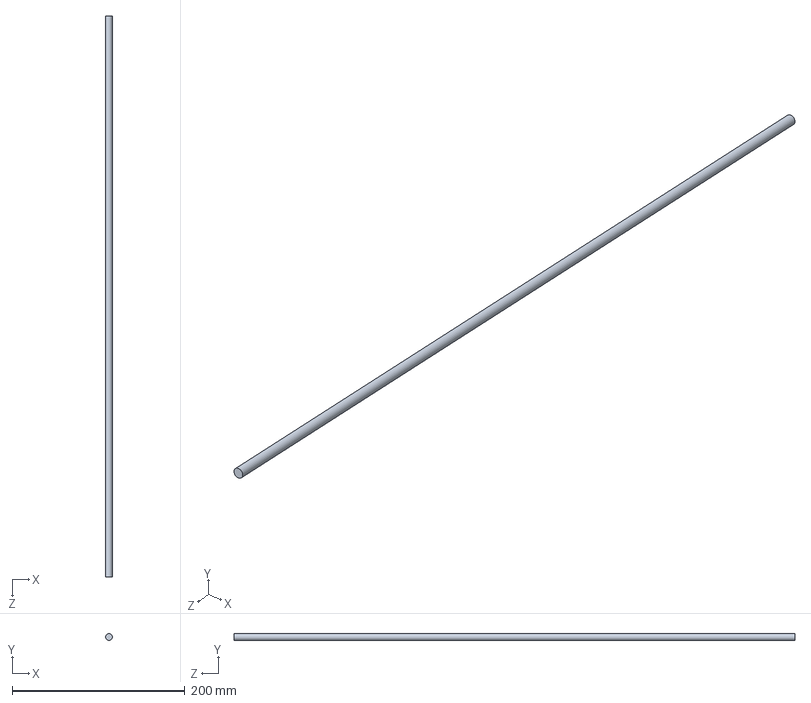
[picture p85: CAD file, 2013-08-03]
MORGAN/MLC-1-008.SLDPRT
8.00 x 8.00 x 650.0 mm
