angrychisel/makelab-chs-MCAPP/MORGAN/Morgan-master/stl/03-z_mount_bottom_8mm.SLDPRT

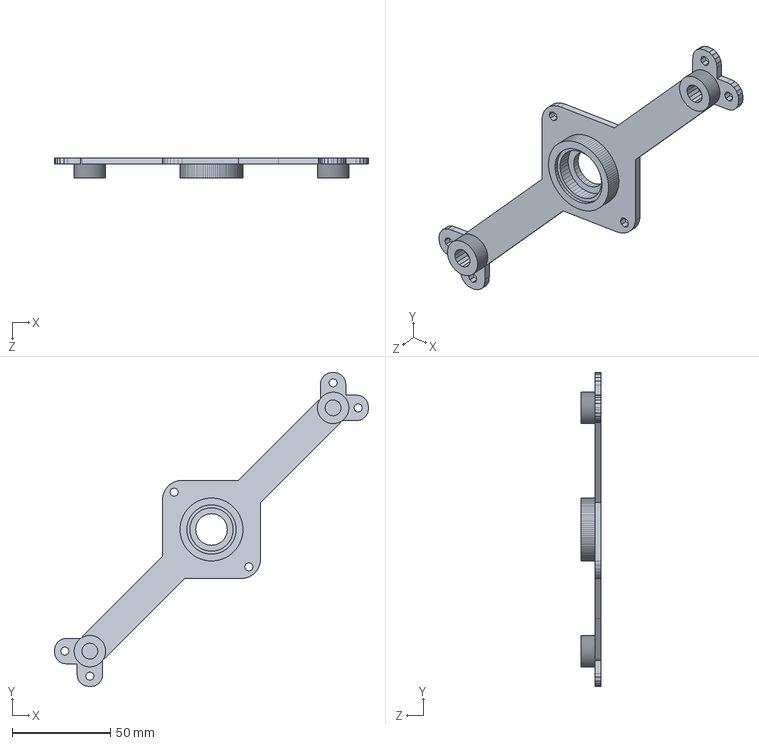
[picture p86: CAD file, 2013-07-25]
MORGAN/Morgan-master/stl/03-z_mount_bottom_8mm.SLDPRT
159.7 x 159.7 x 10.0 mm
