angrychisel/makelab-chs-MCAPP/MORGAN/EXPERIMENTAL/hall_effect_sensor_holder.SLDPRT

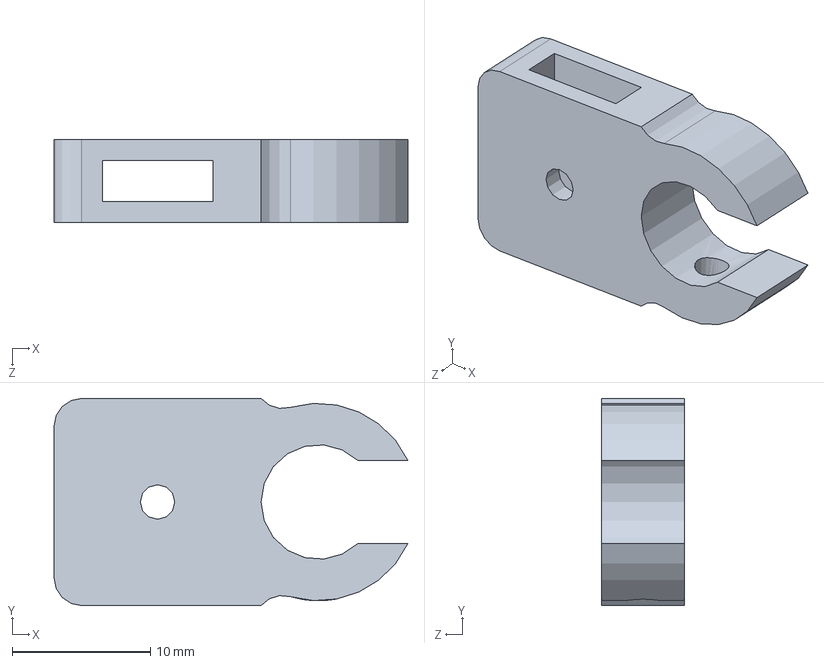
[picture p87: CAD file, 2013-09-09]
MORGAN/EXPERIMENTAL/hall_effect_sensor_holder.SLDPRT
25.6 x 15.0 x 6.00 mm
