angrychisel/makelab-chs-MCAPP/MORGAN/FAB APPROVED STL/MLC-1-030.STL

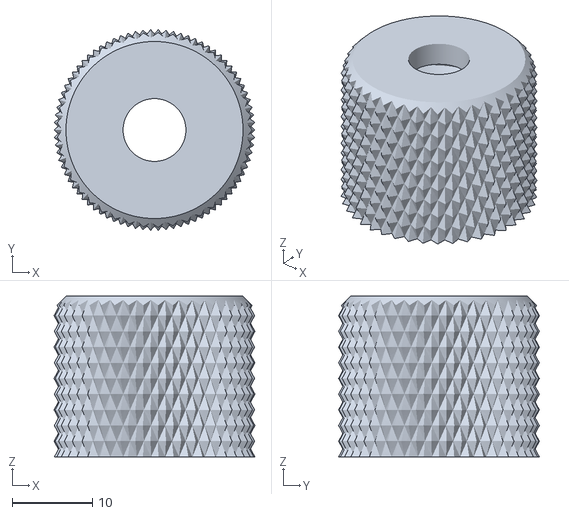
[picture p88: CAD file, 2013-07-29]
MORGAN/FAB APPROVED STL/MLC-1-030.STL
25.0 x 25.0 x 20.0
