angrychisel/makelab-chs-MCAPP/MORGAN/MLC-1-0020.SLDPRT

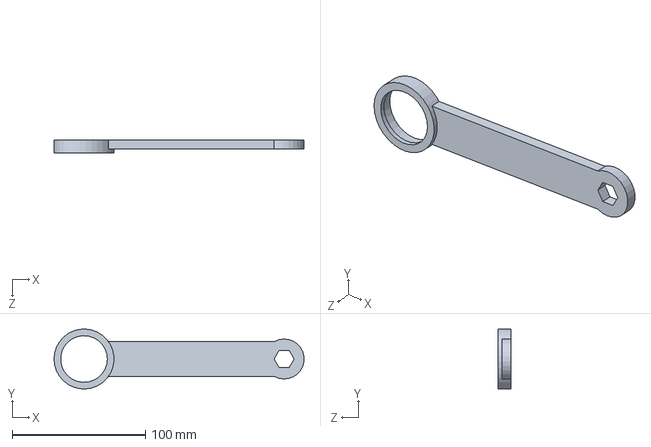
[picture p89: CAD file, 2013-08-01]
MORGAN/MLC-1-0020.SLDPRT
187.4 x 44.9 x 10.0 mm
