angrychisel/makelab-chs-MCAPP/MORGAN/Morgan-master/stl/Eckstruder_Small_Gear_Herringbone.stl

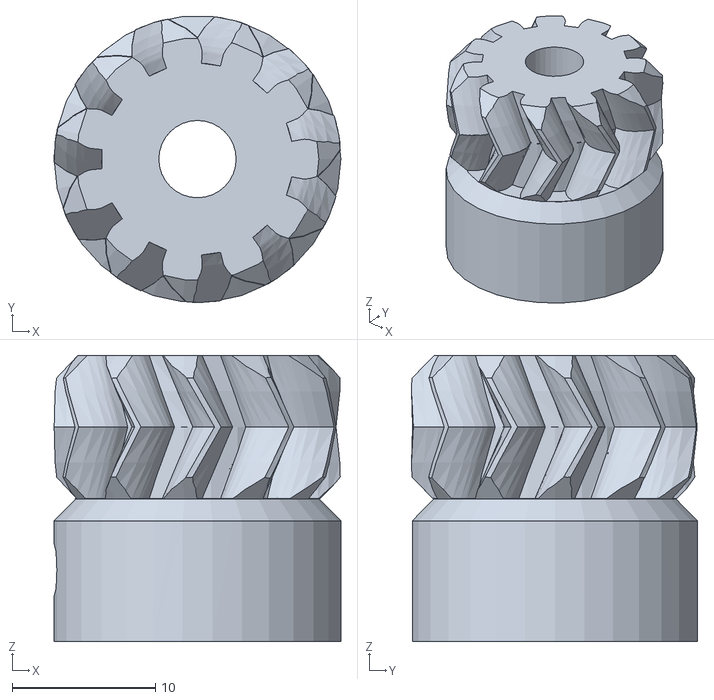
[picture p90: CAD file, 2013-07-25]
MORGAN/Morgan-master/stl/Eckstruder_Small_Gear_Herringbone.stl
20.0 x 20.0 x 20.0
