angrychisel/makelab-chs-MCAPP/MORGAN/EXPERIMENTAL/belt stop.SLDPRT

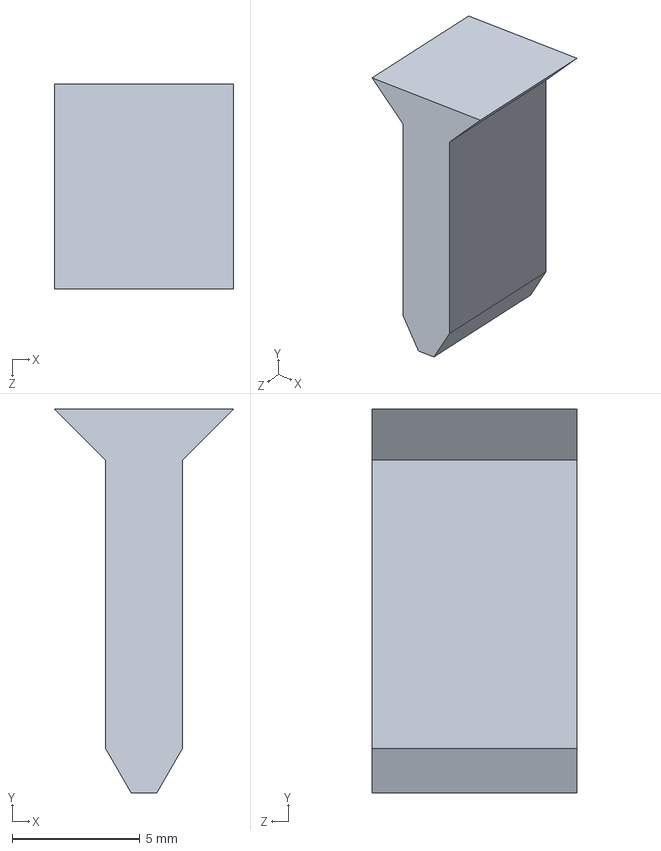
[picture p91: CAD file, 2013-08-17]
MORGAN/EXPERIMENTAL/belt stop.SLDPRT
7.00 x 15.0 x 8.00 mm
