angrychisel/makelab-chs-MCAPP/MORGAN/FAB APPROVED STL/MLC-1-031.STL

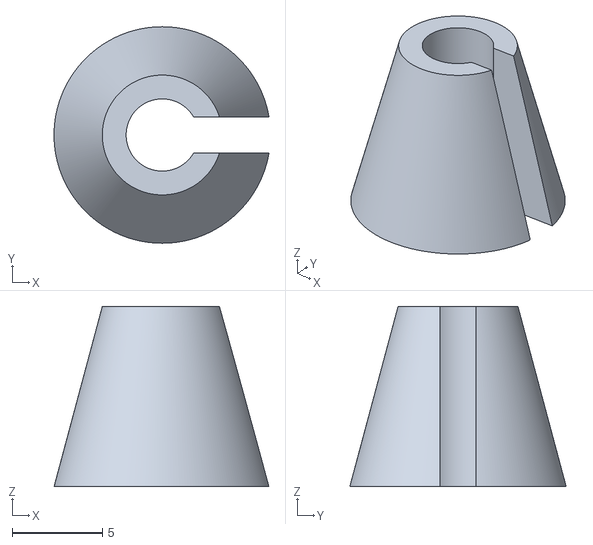
[picture p92: CAD file, 2013-07-29]
MORGAN/FAB APPROVED STL/MLC-1-031.STL
11.9 x 12.0 x 10.0
