angrychisel/makelab-chs-MCAPP/MORGAN/MLC-1-001.SLDPRT

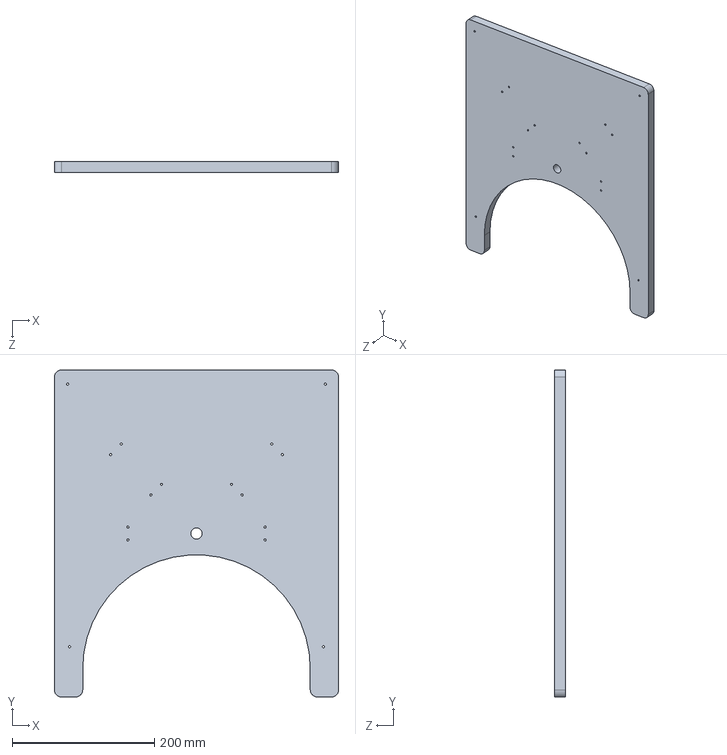
[picture p93: CAD file, 2013-07-30]
MORGAN/MLC-1-001.SLDPRT
400.0 x 460.0 x 15.9 mm
