angrychisel/makelab-chs-MCAPP/MORGAN/Morgan-master/stl/09-22mm_6805_bearing_adaptor.stl

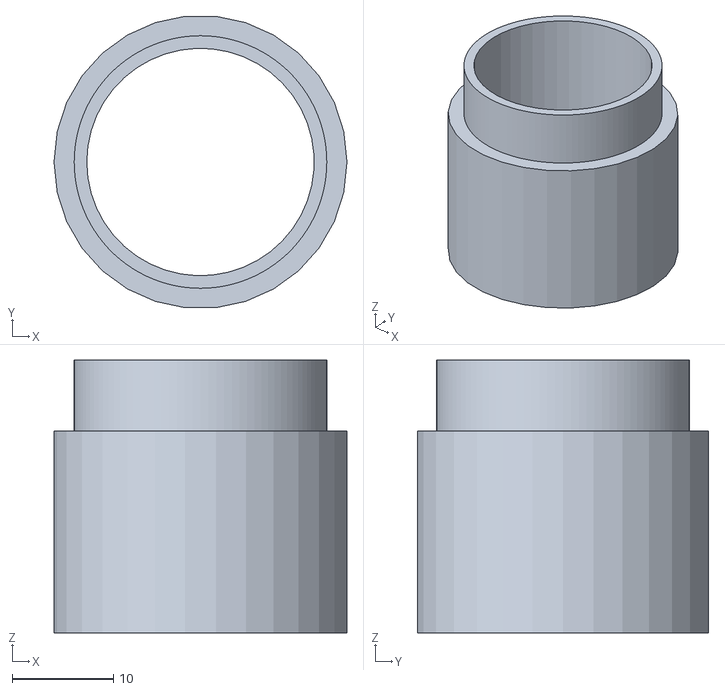
[picture p94: CAD file, 2013-07-25]
MORGAN/Morgan-master/stl/09-22mm_6805_bearing_adaptor.stl
29.0 x 28.8 x 27.0
