angrychisel/makelab-chs-MCAPP/MORGAN/EXPERIMENTAL/belt tensioner.SLDPRT

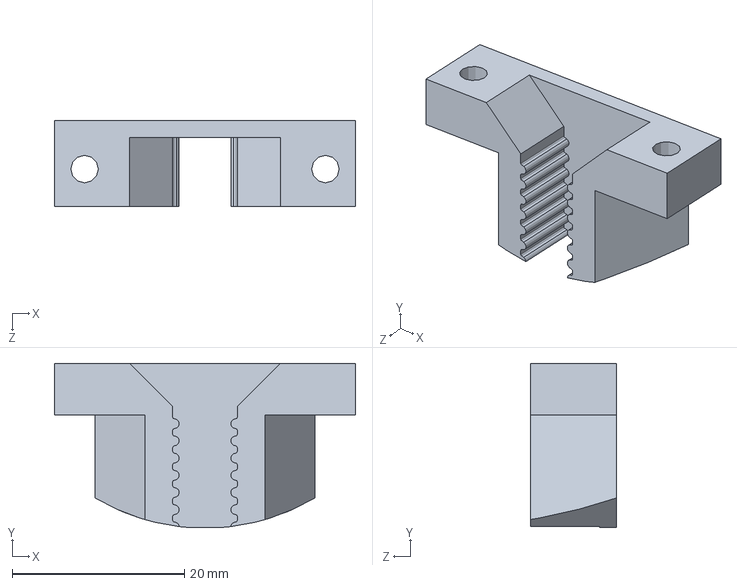
[picture p95: CAD file, 2013-08-17]
MORGAN/EXPERIMENTAL/belt tensioner.SLDPRT
35.0 x 19.1 x 10.0 mm
