angrychisel/makelab-chs-MCAPP/MORGAN/FAB APPROVED STL/MLC-1-0016.STL

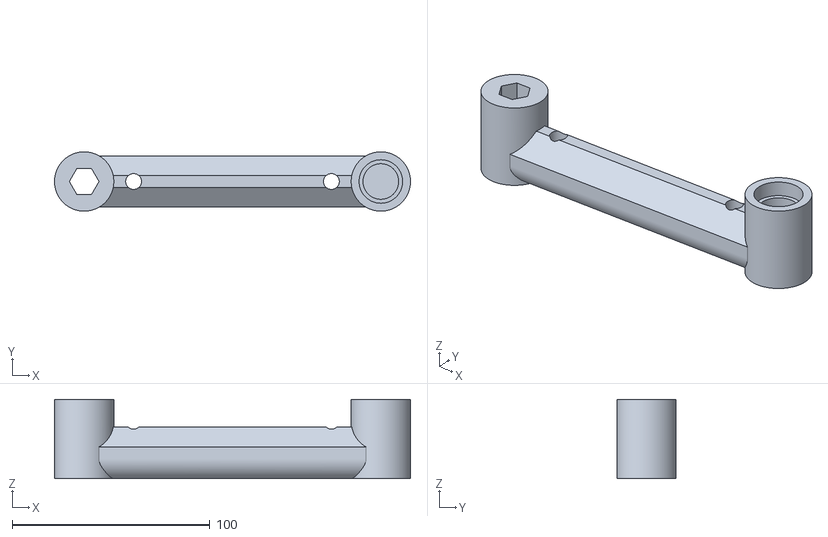
[picture p96: CAD file, 2013-07-29]
MORGAN/FAB APPROVED STL/MLC-1-0016.STL
180.0 x 30.0 x 40.0
