angrychisel/makelab-chs-MCAPP/MORGAN/MLC-1-002.SLDPRT

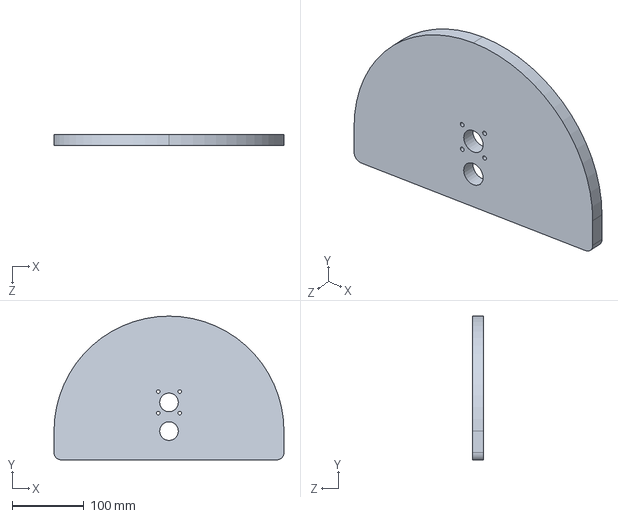
[picture p97: CAD file, 2013-07-30]
MORGAN/MLC-1-002.SLDPRT
320.0 x 200.0 x 15.9 mm
