angrychisel/makelab-chs-MCAPP/MORGAN/Morgan-master/stl/15-hall_endstop_holder.stl

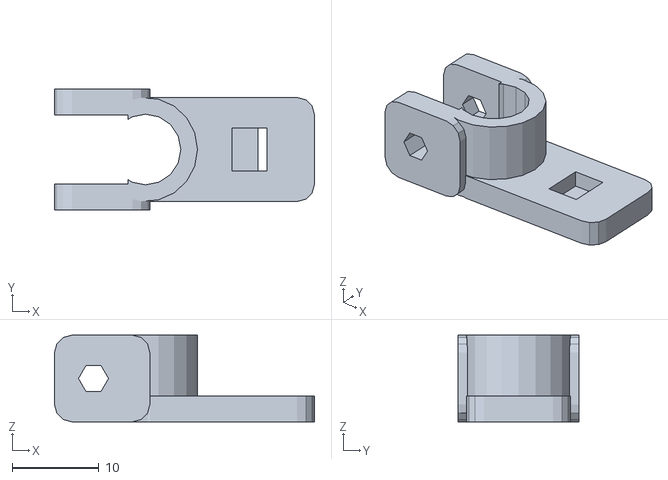
[picture p98: CAD file, 2013-07-25]
MORGAN/Morgan-master/stl/15-hall_endstop_holder.stl
30.0 x 14.0 x 10.0
