angrychisel/makelab-chs-MCAPP/MORGAN/continous stud_am.sldprt

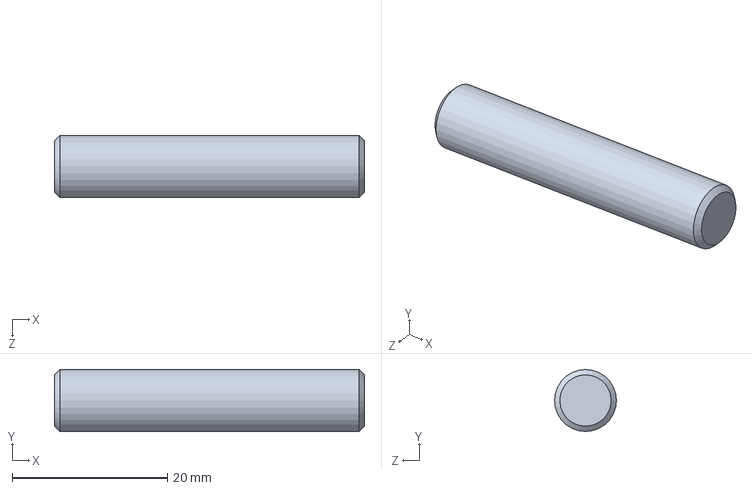
[picture p99: CAD file, 2013-07-30]
MORGAN/continous stud_am.sldprt
40.0 x 8.00 x 8.00 mm
