angrychisel/makelab-chs-MCAPP/MORGAN/Morgan-master/stl/12-bed_z_mount_bracket.stl

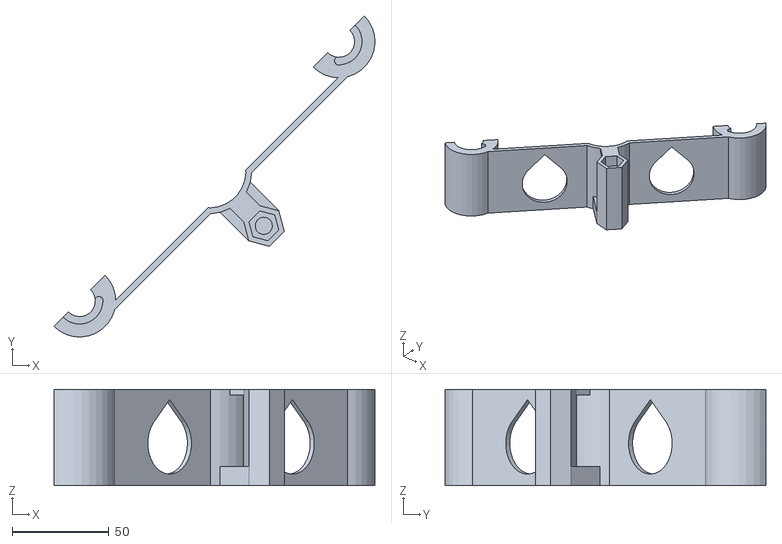
[picture p100: CAD file, 2013-07-25]
MORGAN/Morgan-master/stl/12-bed_z_mount_bracket.stl
166.3 x 166.3 x 50.0
