angrychisel/makelab-chs-MCAPP/MORGAN/EXPERIMENTAL/belt tensioner bottom.SLDPRT

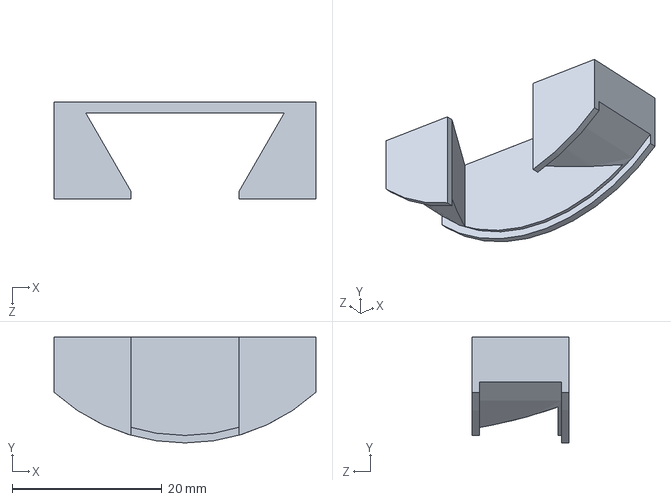
[picture p101: CAD file, 2013-08-17]
MORGAN/EXPERIMENTAL/belt tensioner bottom.SLDPRT
35.0 x 14.1 x 13.0 mm
