angrychisel/makelab-chs-MCAPP/MORGAN/FAB APPROVED STL/MLC-1-0027.STL

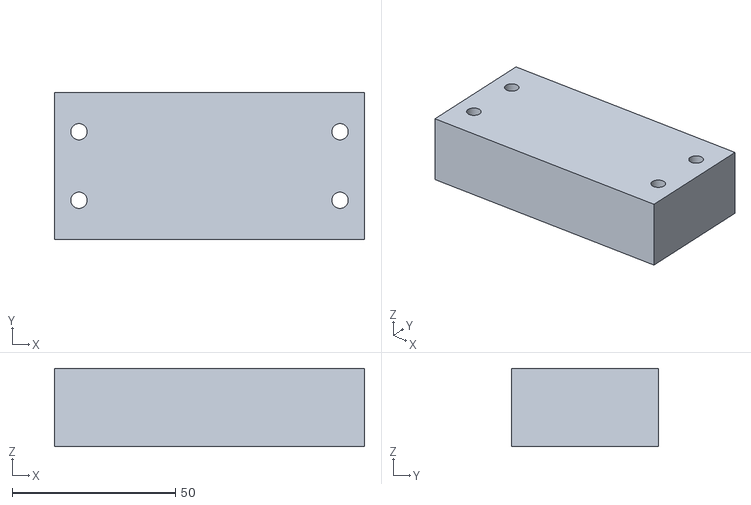
[picture p102: CAD file, 2013-07-27]
MORGAN/FAB APPROVED STL/MLC-1-0027.STL
95.0 x 45.0 x 24.0
