angrychisel/makelab-chs-MCAPP/MORGAN/Morgan-master/stl/21-Morgan_toolhead.stl

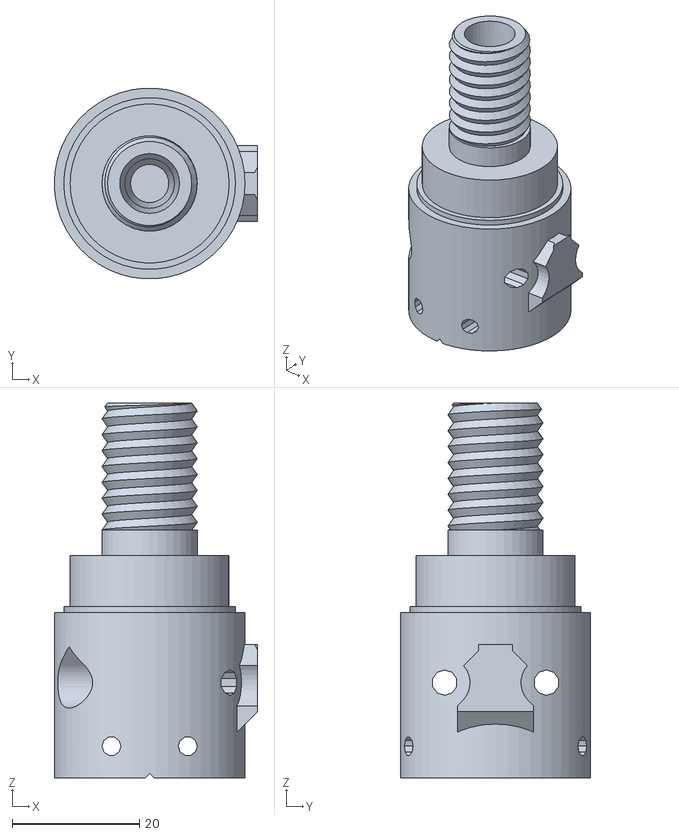
[picture p103: CAD file, 2013-07-25]
MORGAN/Morgan-master/stl/21-Morgan_toolhead.stl
32.0 x 29.9 x 59.0
