angrychisel/makelab-chs-MCAPP/MORGAN/EXPERIMENTAL/MLCE-1-002.SLDPRT

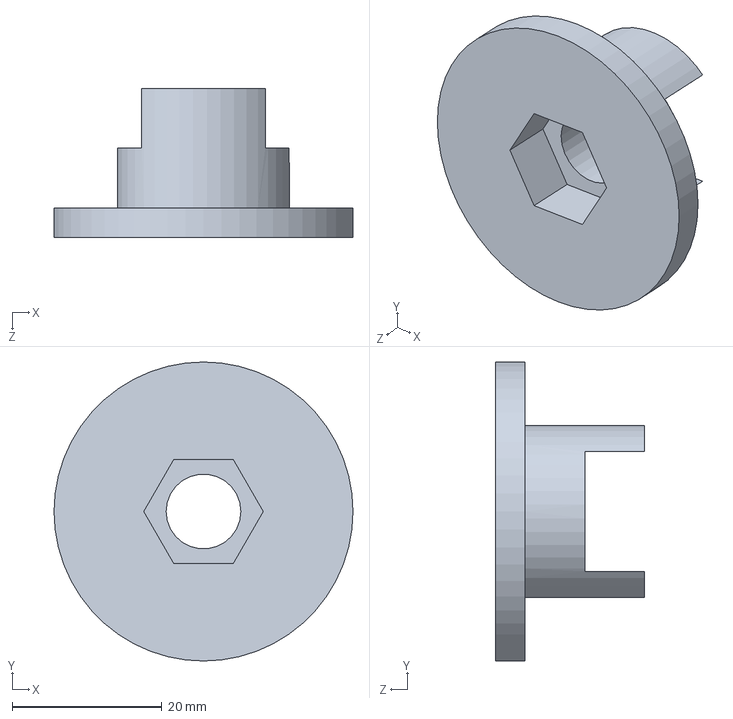
[picture p104: CAD file, 2013-07-30]
MORGAN/EXPERIMENTAL/MLCE-1-002.SLDPRT
40.0 x 40.0 x 20.0 mm
