angrychisel/makelab-chs-MCAPP/MORGAN/FAB APPROVED STL/MLC-1-0025.STL

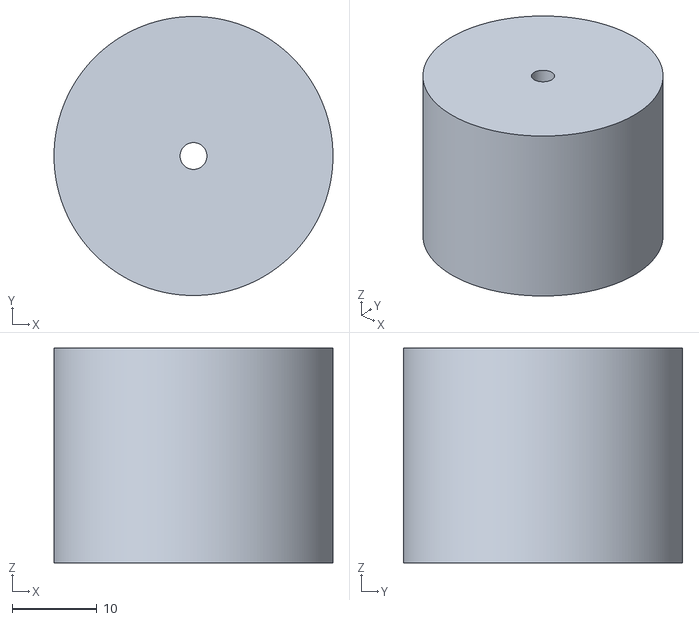
[picture p105: CAD file, 2013-07-27]
MORGAN/FAB APPROVED STL/MLC-1-0025.STL
33.0 x 33.0 x 25.4
