angrychisel/makelab-chs-MCAPP/MORGAN/Morgan-master/stl/02-pvc_pipe_support_b.stl

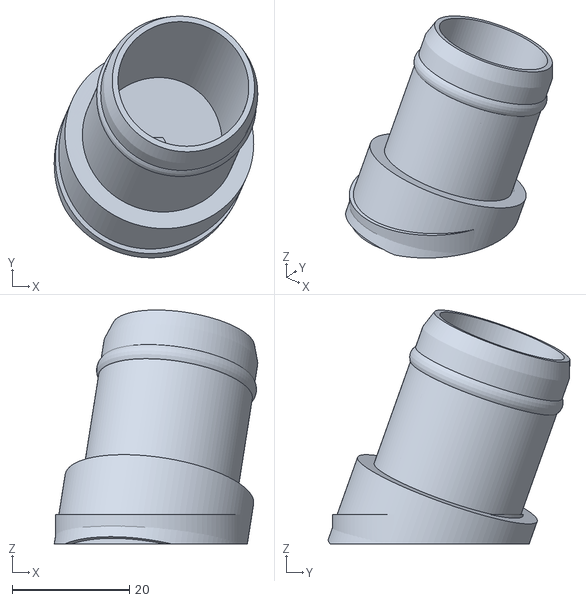
[picture p106: CAD file, 2013-07-25]
MORGAN/Morgan-master/stl/02-pvc_pipe_support_b.stl
34.7 x 41.2 x 39.9
