angrychisel/makelab-chs-MCAPP/MORGAN/radial ball bearing_68_skf.sldprt

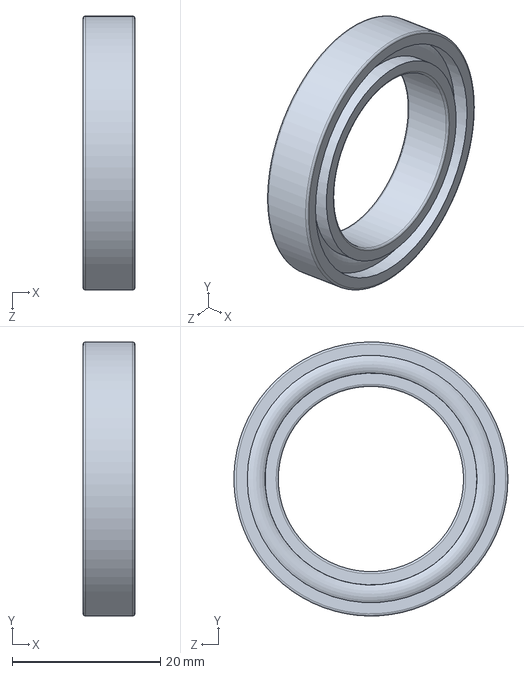
[picture p107: CAD file, 2013-07-30]
MORGAN/radial ball bearing_68_skf.sldprt
7.00 x 37.0 x 37.0 mm
