angrychisel/makelab-chs-MCAPP/MORGAN/EXPERIMENTAL/MLCE-1-001.SLDPRT

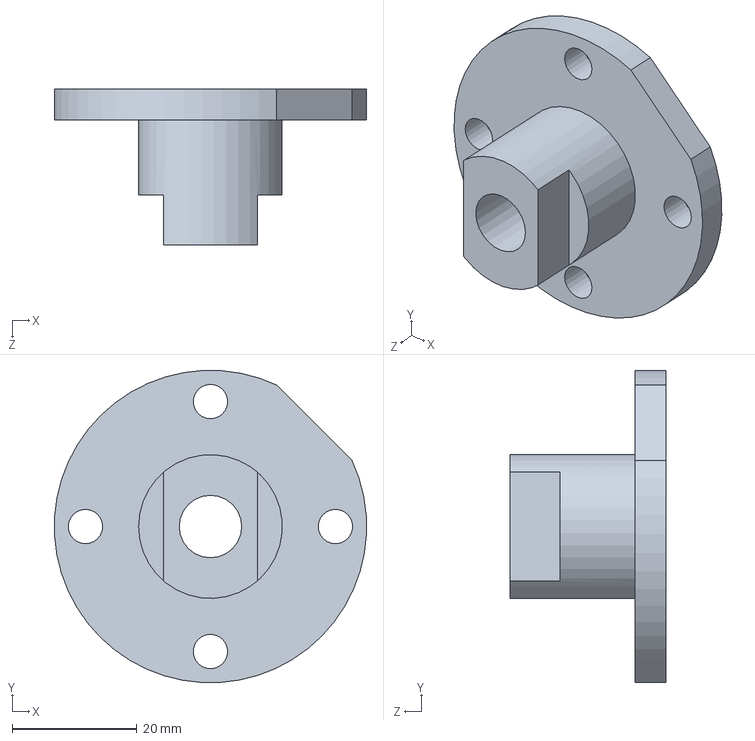
[picture p108: CAD file, 2013-07-30]
MORGAN/EXPERIMENTAL/MLCE-1-001.SLDPRT
49.9 x 49.9 x 25.0 mm
