angrychisel/makelab-chs-MCAPP/MORGAN/FAB APPROVED STL/MLC-1-0028.STL

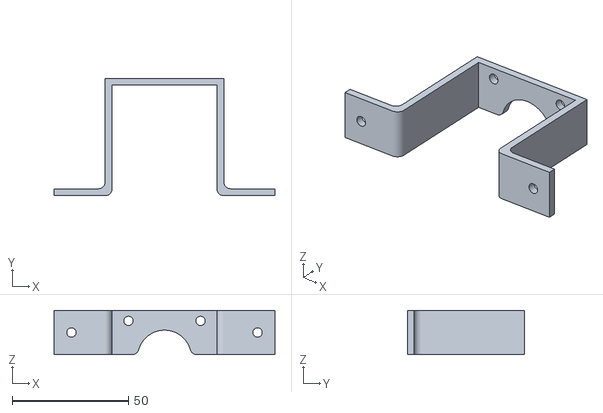
[picture p109: CAD file, 2013-07-27]
MORGAN/FAB APPROVED STL/MLC-1-0028.STL
95.0 x 50.5 x 19.0
