angrychisel/makelab-chs-MCAPP/MORGAN/Morgan-master/stl/11-bed_arm_right_8mm.stl

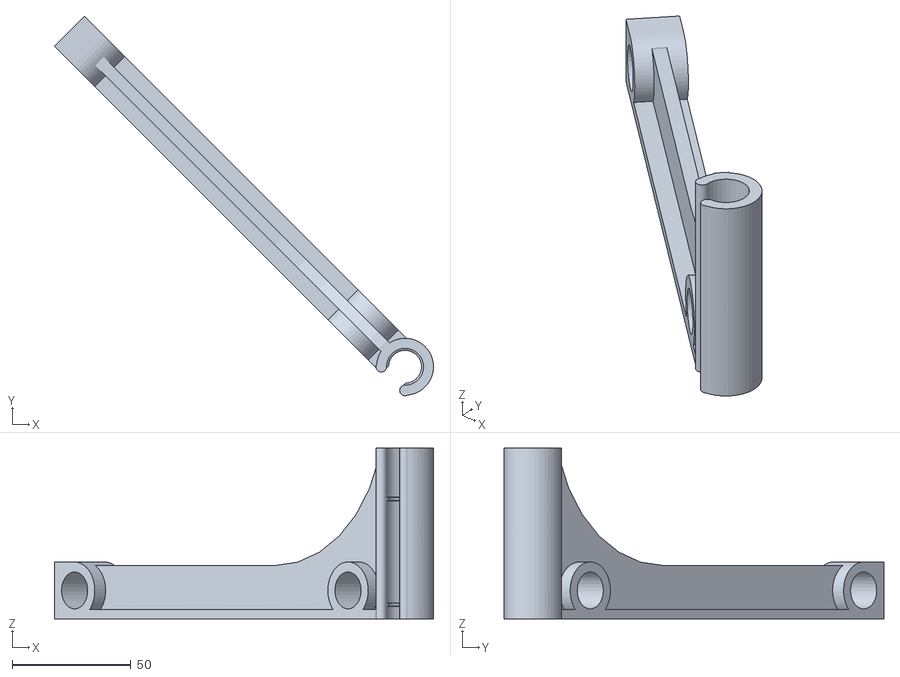
[picture p110: CAD file, 2013-07-25]
MORGAN/Morgan-master/stl/11-bed_arm_right_8mm.stl
159.8 x 160.0 x 72.0
