angrychisel/makelab-chs-MCAPP/MORGAN/FAB APPROVED STL/MLC-1-0021.STL

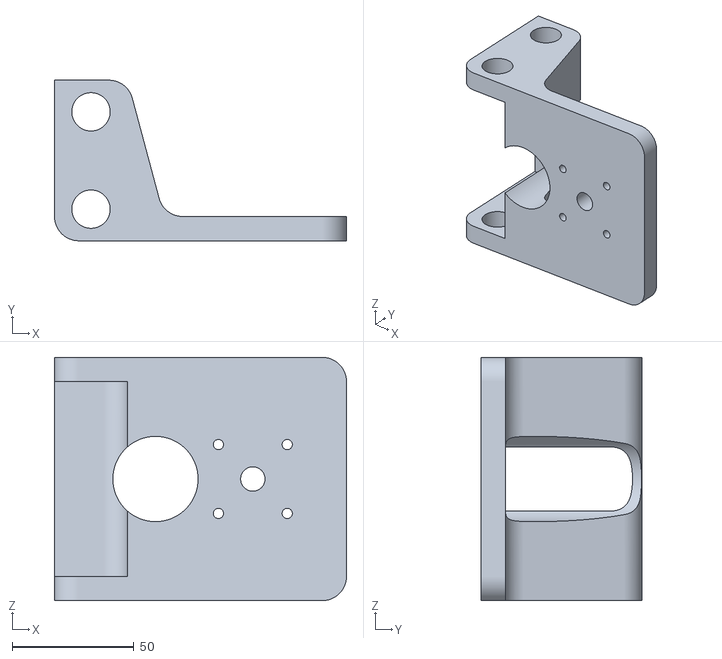
[picture p111: CAD file, 2013-07-27]
MORGAN/FAB APPROVED STL/MLC-1-0021.STL
120.0 x 66.0 x 100.0
