angrychisel/makelab-chs-MCAPP/MORGAN/Morgan-master/stl/20-Morgan_arm_Theta_b.stl

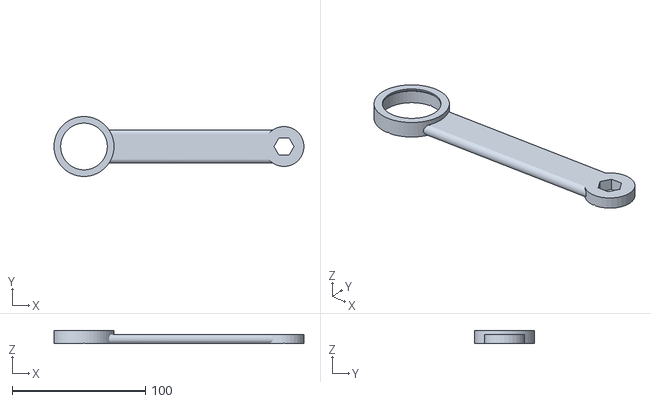
[picture p112: CAD file, 2013-07-25]
MORGAN/Morgan-master/stl/20-Morgan_arm_Theta_b.stl
187.5 x 44.9 x 10.0
