angrychisel/makelab-chs-MCAPP/MORGAN/FAB APPROVED STL/MLC-1-006.STL

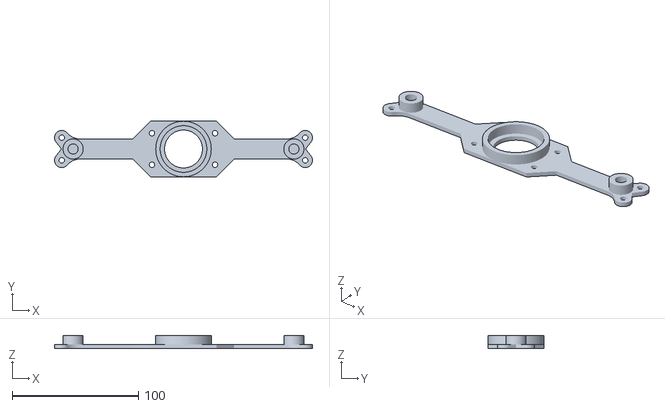
[picture p113: CAD file, 2013-07-27]
MORGAN/FAB APPROVED STL/MLC-1-006.STL
204.5 x 44.0 x 10.0
