angrychisel/makelab-chs-MCAPP/MORGAN/Morgan-master/stl/13-bed_rear_mountclips.stl

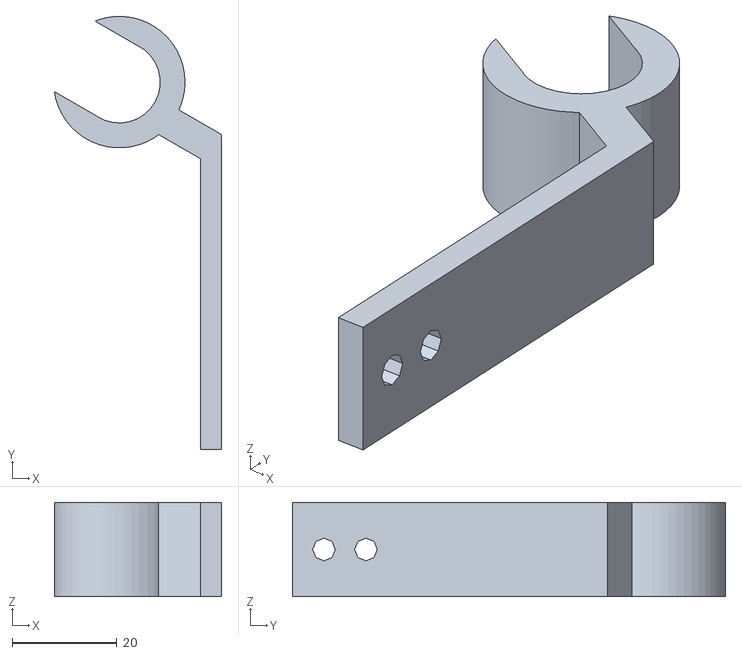
[picture p114: CAD file, 2013-07-25]
MORGAN/Morgan-master/stl/13-bed_rear_mountclips.stl
31.9 x 82.5 x 18.0
