angrychisel/makelab-chs-MCAPP/MORGAN/EXPERIMENTAL/MLC-1-024.SLDPRT

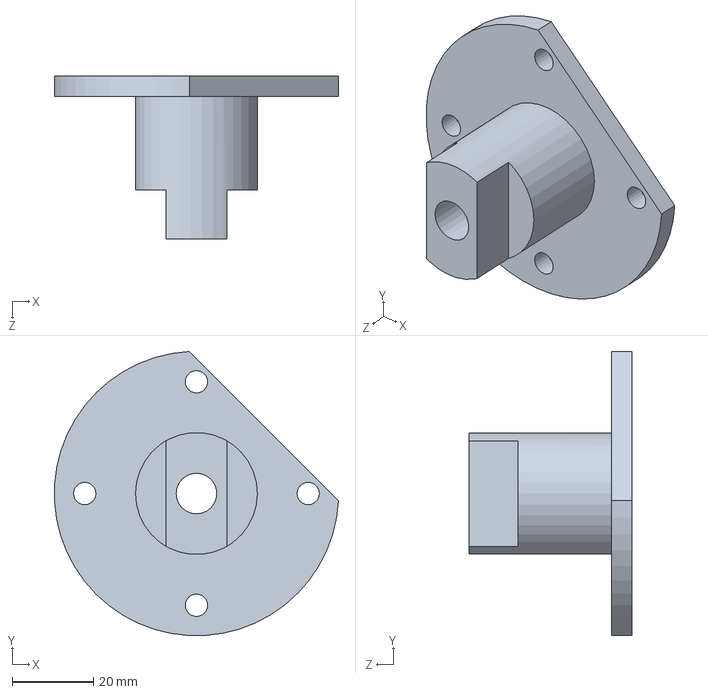
[picture p115: CAD file, 2013-07-26]
MORGAN/EXPERIMENTAL/MLC-1-024.SLDPRT
69.9 x 69.9 x 40.0 mm
