angrychisel/makelab-chs-MCAPP/MORGAN/FAB APPROVED STL/MLC-1-005.STL

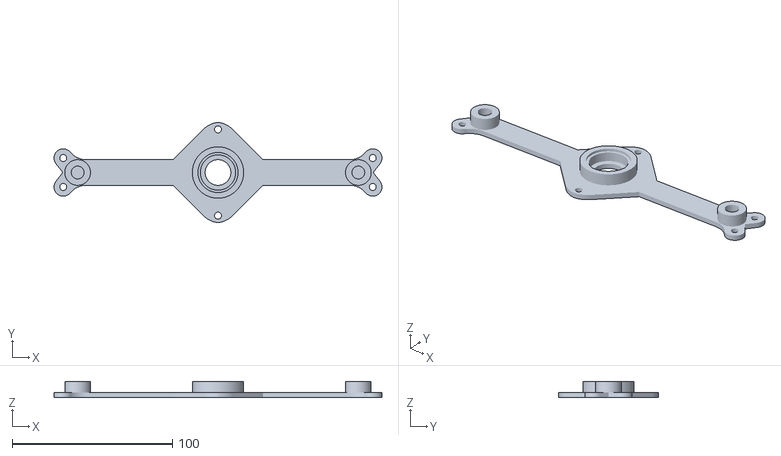
[picture p116: CAD file, 2013-07-27]
MORGAN/FAB APPROVED STL/MLC-1-005.STL
204.5 x 62.5 x 10.0
