angrychisel/makelab-chs-MCAPP/MORGAN/Morgan-master/stl/Eckstruder_Idler_Block_for_Prusa.stl

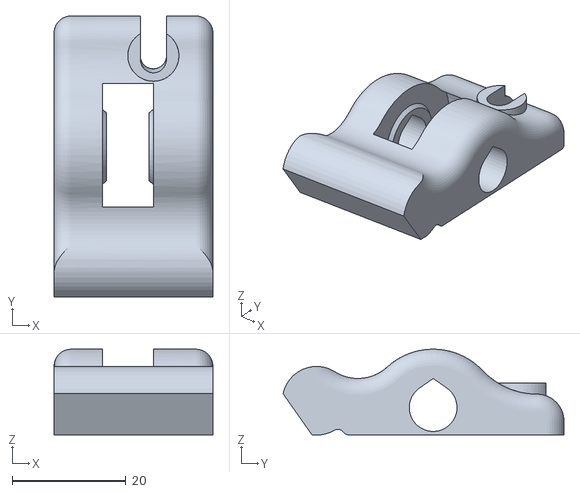
[picture p117: CAD file, 2013-07-25]
MORGAN/Morgan-master/stl/Eckstruder_Idler_Block_for_Prusa.stl
28.0 x 49.5 x 15.1
