angrychisel/makelab-chs-MCAPP/MORGAN/Morgan-master/stl/thumb_knob_M4_extruder.stl

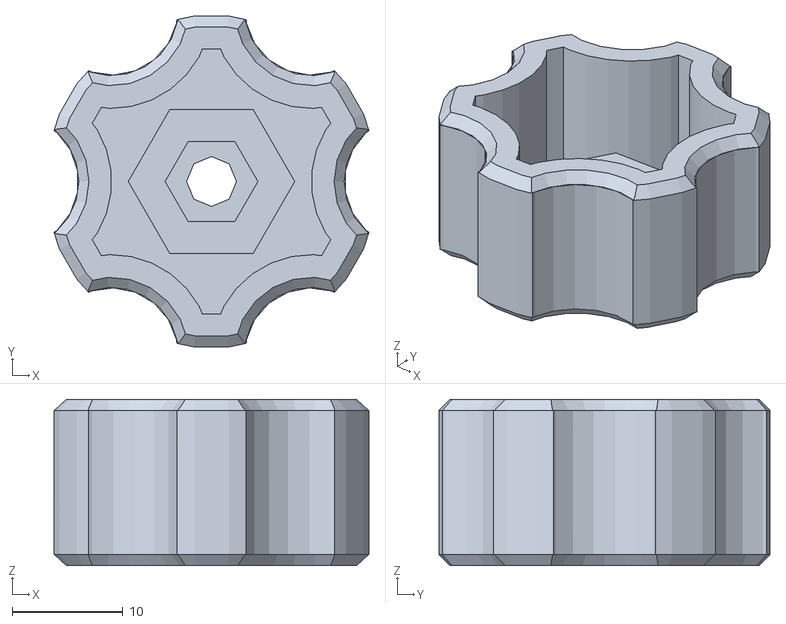
[picture p118: CAD file, 2013-07-25]
MORGAN/Morgan-master/stl/thumb_knob_M4_extruder.stl
28.4 x 29.8 x 15.0
