angrychisel/makelab-chs-MCAPP/MORGAN/EXPERIMENTAL/MLC-1-023.SLDPRT

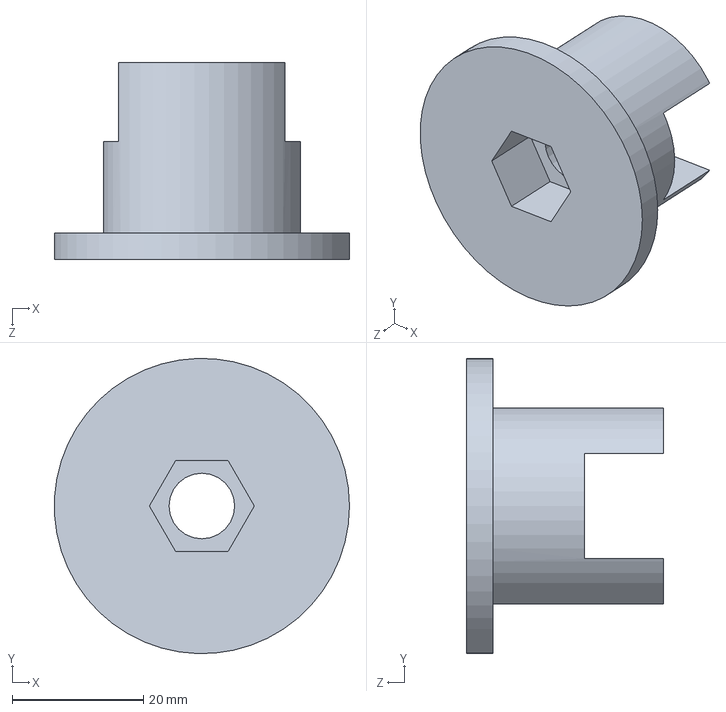
[picture p119: CAD file, 2013-07-26]
MORGAN/EXPERIMENTAL/MLC-1-023.SLDPRT
45.0 x 45.0 x 30.0 mm
