angrychisel/makelab-chs-MCAPP/MORGAN/Morgan-master/stl/18-Morgan_arm_PSI_b.stl

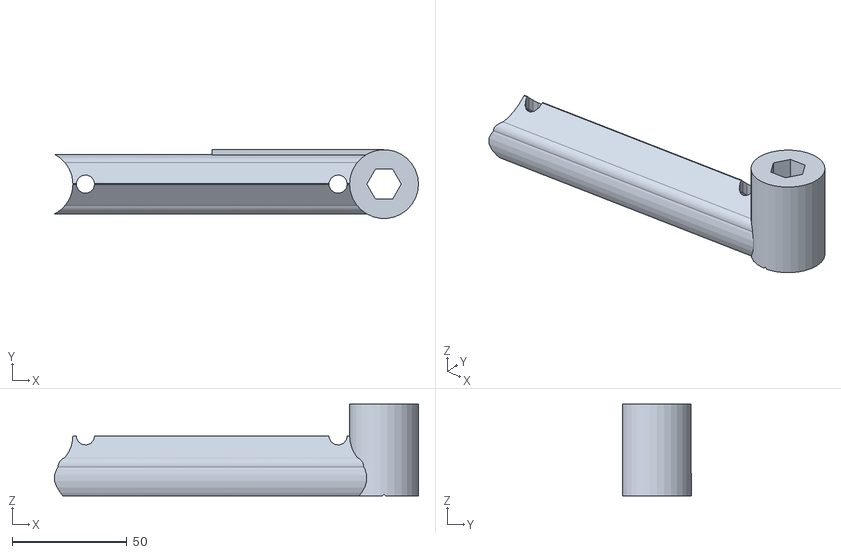
[picture p120: CAD file, 2013-07-25]
MORGAN/Morgan-master/stl/18-Morgan_arm_PSI_b.stl
158.5 x 29.9 x 40.0
