angrychisel/makelab-chs-MCAPP/MORGAN/Morgan-master/stl/03-z_mount_bottom_12mm.stl

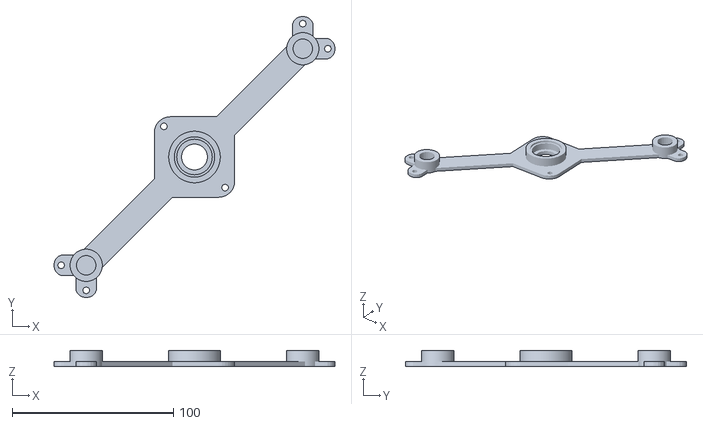
[picture p121: CAD file, 2013-07-25]
MORGAN/Morgan-master/stl/03-z_mount_bottom_12mm.stl
174.3 x 174.3 x 10.0
