angrychisel/makelab-chs-MCAPP/MORGAN/MLC-1-031.SLDPRT

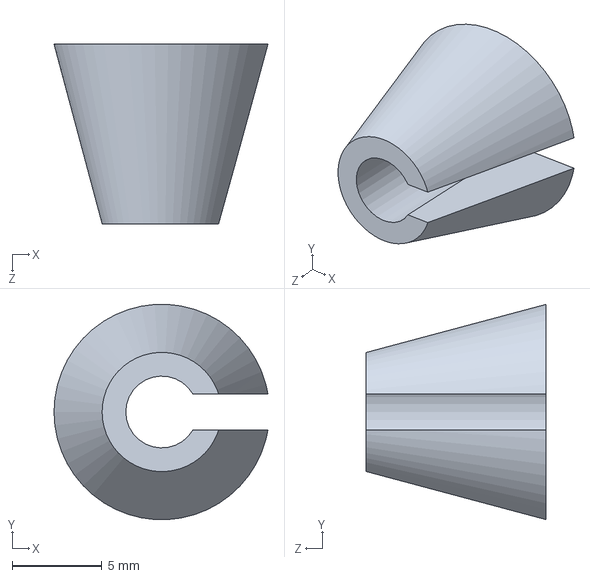
[picture p122: CAD file, 2013-07-29]
MORGAN/MLC-1-031.SLDPRT
11.9 x 12.0 x 10.0 mm
