angrychisel/makelab-chs-MCAPP/MORGAN/MLC-1-0016.SLDPRT

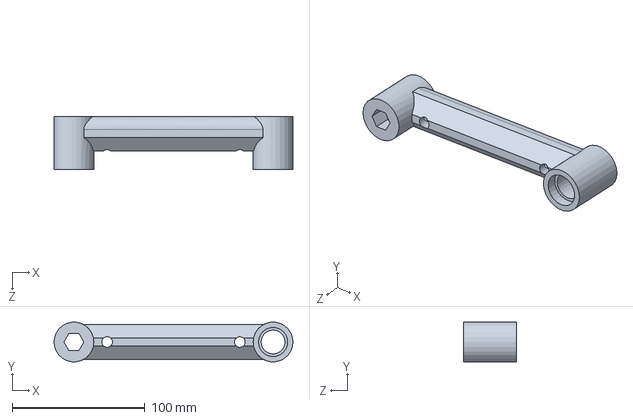
[picture p123: CAD file, 2013-07-29]
MORGAN/MLC-1-0016.SLDPRT
180.0 x 29.8 x 40.0 mm
