angrychisel/makelab-chs-MCAPP/MORGAN/Morgan-master/stl/11-bed_arm_right_12mm.stl

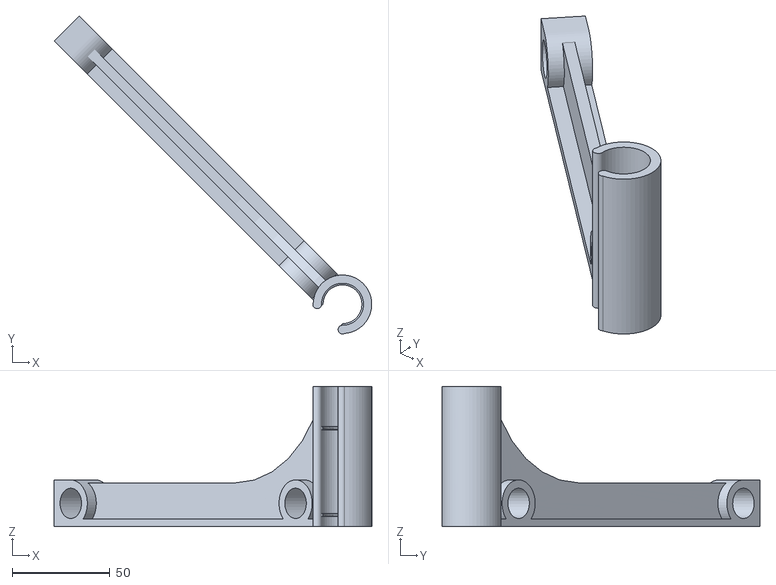
[picture p124: CAD file, 2013-07-25]
MORGAN/Morgan-master/stl/11-bed_arm_right_12mm.stl
162.8 x 163.0 x 72.0
