angrychisel/makelab-chs-MCAPP/MORGAN/JHEAD NOZZLE.SLDPRT

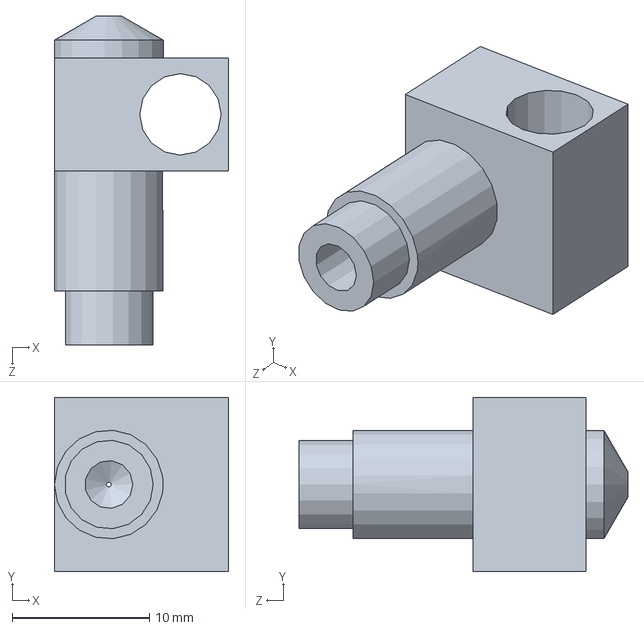
[picture p125: CAD file, 2013-07-28]
MORGAN/JHEAD NOZZLE.SLDPRT
12.7 x 12.7 x 24.0 mm
