angrychisel/makelab-chs-MCAPP/MORGAN/Morgan-master/stl/tighteningCone_2.stl

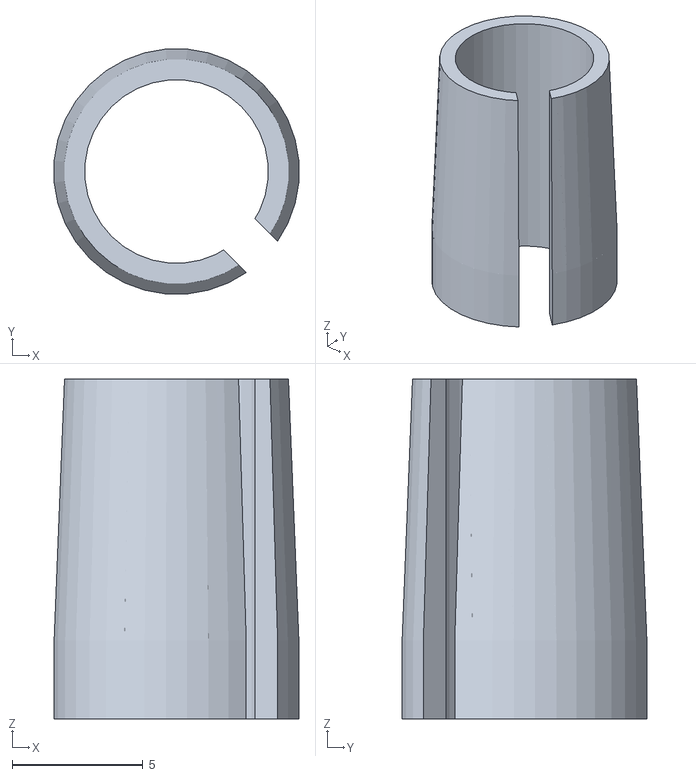
[picture p126: CAD file, 2013-07-25]
MORGAN/Morgan-master/stl/tighteningCone_2.stl
9.37 x 9.37 x 13.0
