angrychisel/makelab-chs-MCAPP/MORGAN/Untitled.stl

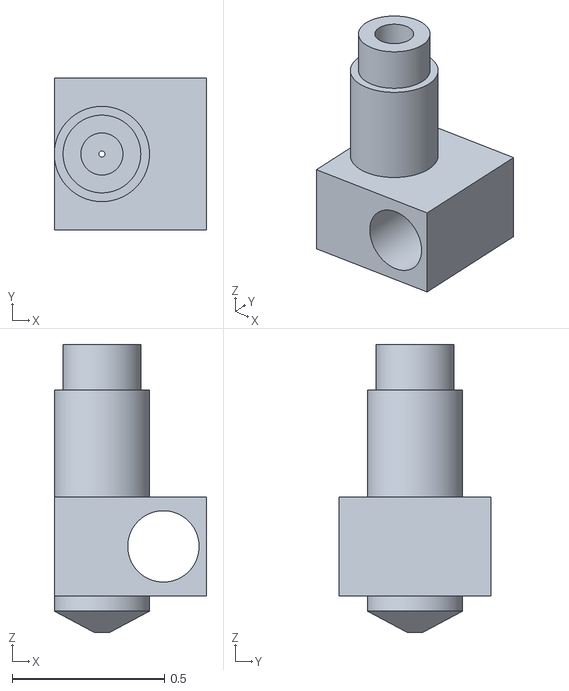
[picture p127: CAD file, 2013-07-28]
MORGAN/Untitled.stl
0.5 x 0.5 x 0.945
