angrychisel/makelab-chs-MCAPP/MORGAN/JHEAD.SLDPRT

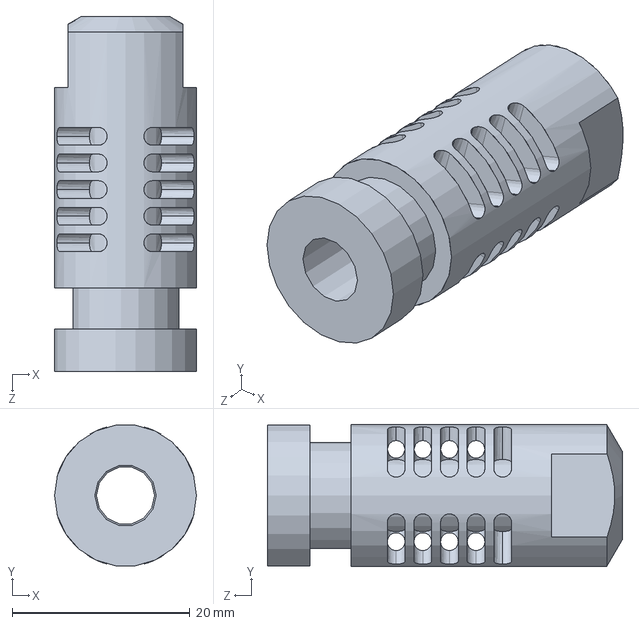
[picture p128: CAD file, 2013-07-28]
MORGAN/JHEAD.SLDPRT
16.0 x 16.0 x 40.0 mm
