angrychisel/makelab-chs-MCAPP/MORGAN/MLC-1-007.SLDPRT

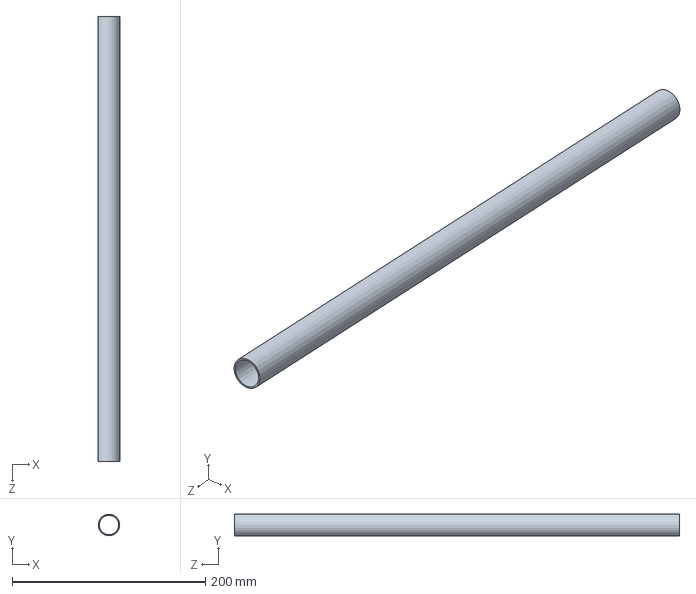
[picture p129: CAD file, 2013-07-28]
MORGAN/MLC-1-007.SLDPRT
22.2 x 22.2 x 460.0 mm
