angrychisel/makelab-chs-MCAPP/MORGAN/Morgan-master/stl/05-motormount_short.stl

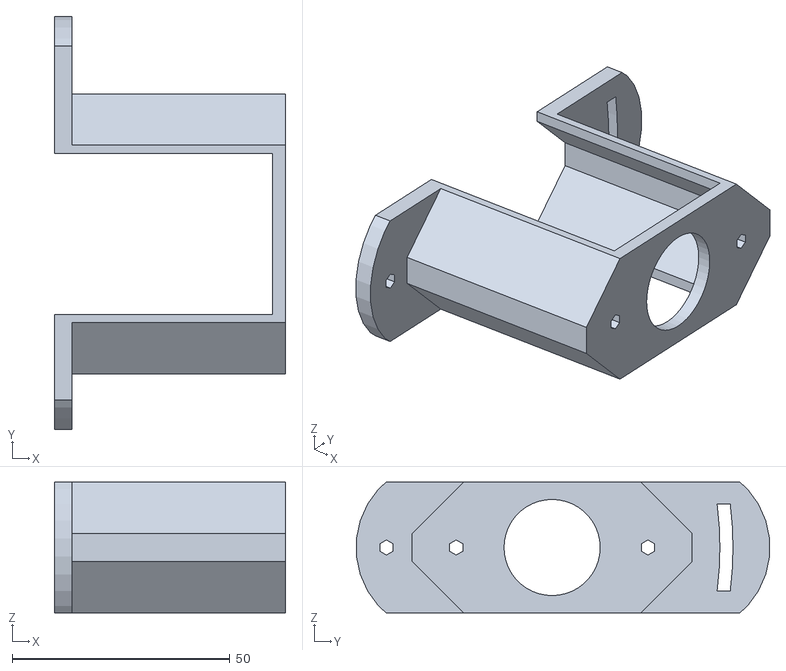
[picture p130: CAD file, 2013-07-25]
MORGAN/Morgan-master/stl/05-motormount_short.stl
53.0 x 94.8 x 30.0
