angrychisel/makelab-chs-MCAPP/MORGAN/MLC-1-0010.SLDPRT

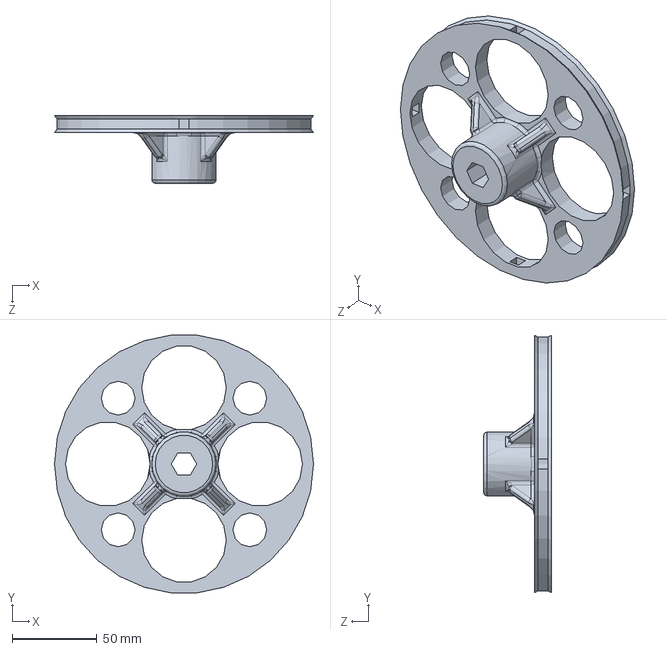
[picture p131: CAD file, 2013-07-27]
MORGAN/MLC-1-0010.SLDPRT
153.0 x 152.2 x 40.0 mm
