angrychisel/makelab-chs-MCAPP/MORGAN/Morgan-master/stl/04-z_mount_top_12mm.stl

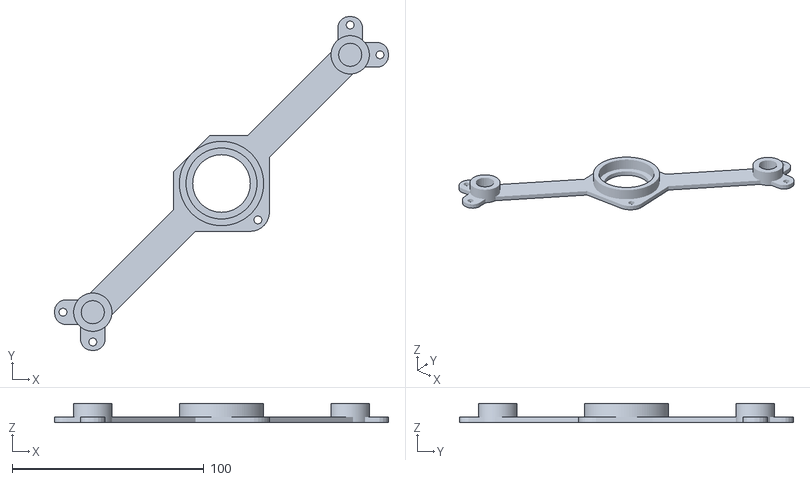
[picture p132: CAD file, 2013-07-25]
MORGAN/Morgan-master/stl/04-z_mount_top_12mm.stl
174.3 x 174.3 x 10.0
