angrychisel/makelab-chs-MCAPP/MORGAN/Morgan-master/stl/06-motormount_tall.stl

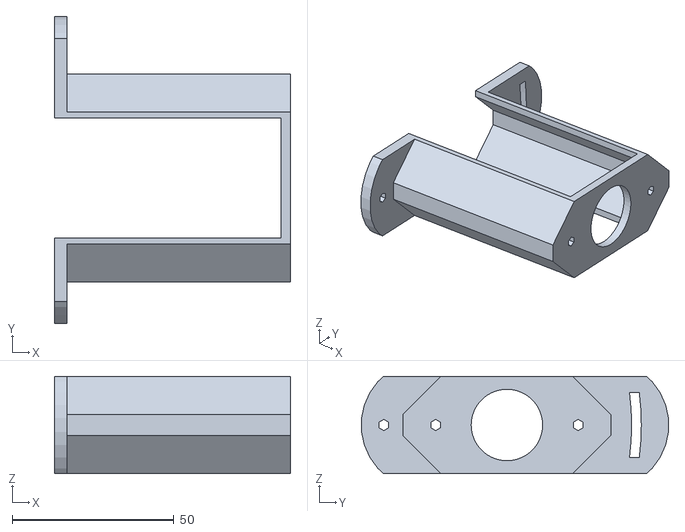
[picture p133: CAD file, 2013-07-25]
MORGAN/Morgan-master/stl/06-motormount_tall.stl
73.0 x 94.8 x 30.0
