angrychisel/makelab-chs-MCAPP/MORGAN/Morgan-master/stl/Eckstruder_Big_Gear_Herringbone.stl

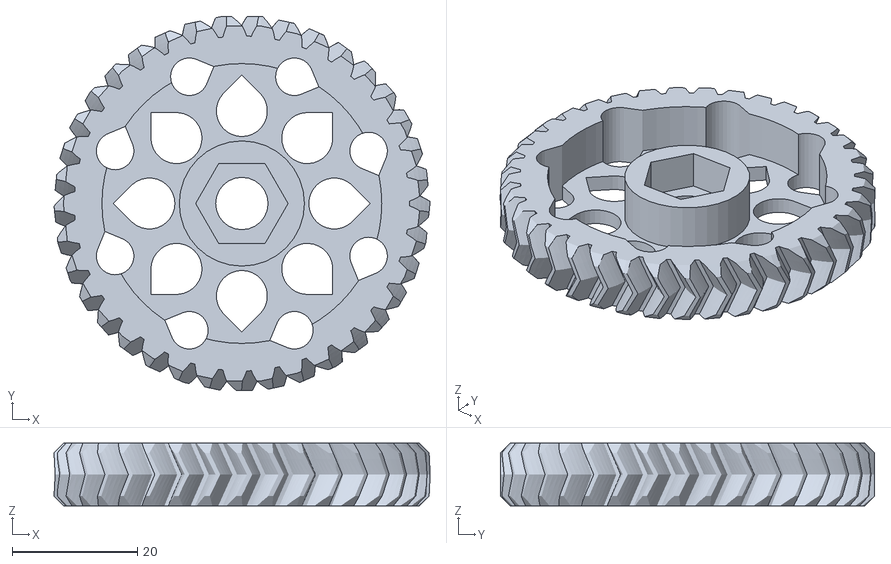
[picture p134: CAD file, 2013-07-25]
MORGAN/Morgan-master/stl/Eckstruder_Big_Gear_Herringbone.stl
60.1 x 59.8 x 10.0
