angrychisel/makelab-chs-MCAPP/MORGAN/MLC-1-0026.SLDPRT

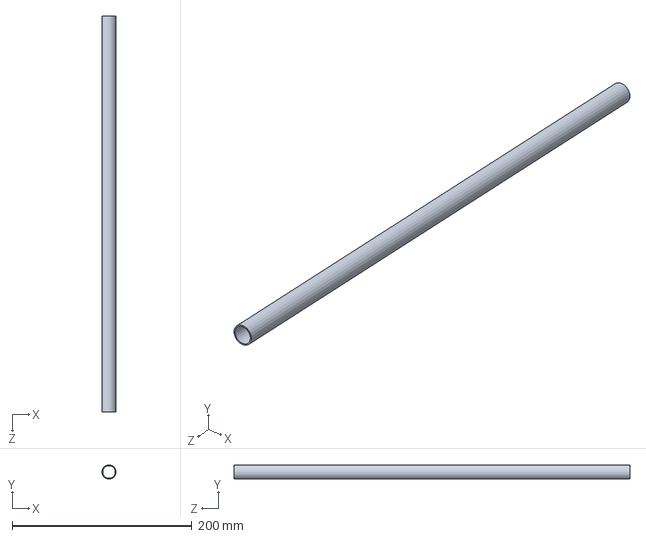
[picture p135: CAD file, 2013-07-26]
MORGAN/MLC-1-0026.SLDPRT
15.9 x 15.9 x 440.0 mm
