angrychisel/makelab-chs-MCAPP/MORGAN/Morgan-master/stl/14-bed_front_mountclips.stl

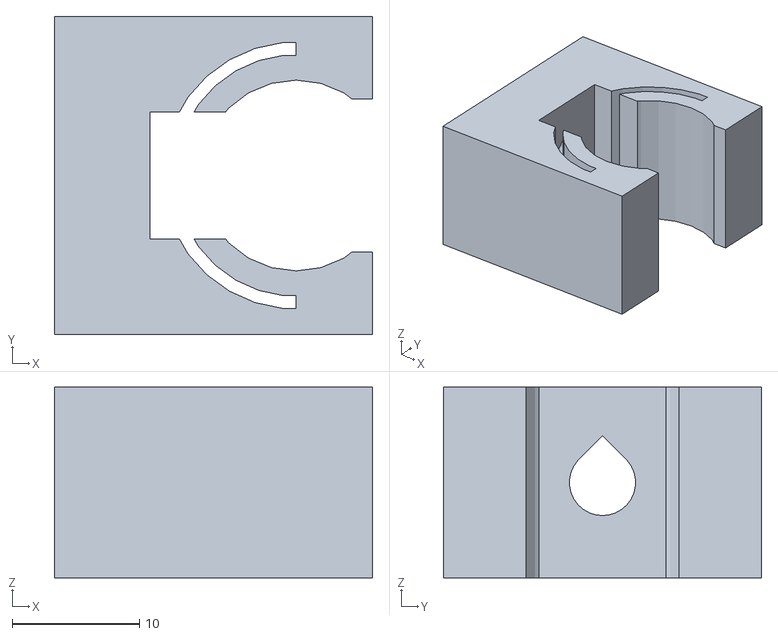
[picture p136: CAD file, 2013-07-25]
MORGAN/Morgan-master/stl/14-bed_front_mountclips.stl
25.0 x 25.0 x 15.0
