angrychisel/makelab-chs-MCAPP/MORGAN/MLC-1-0022.SLDPRT

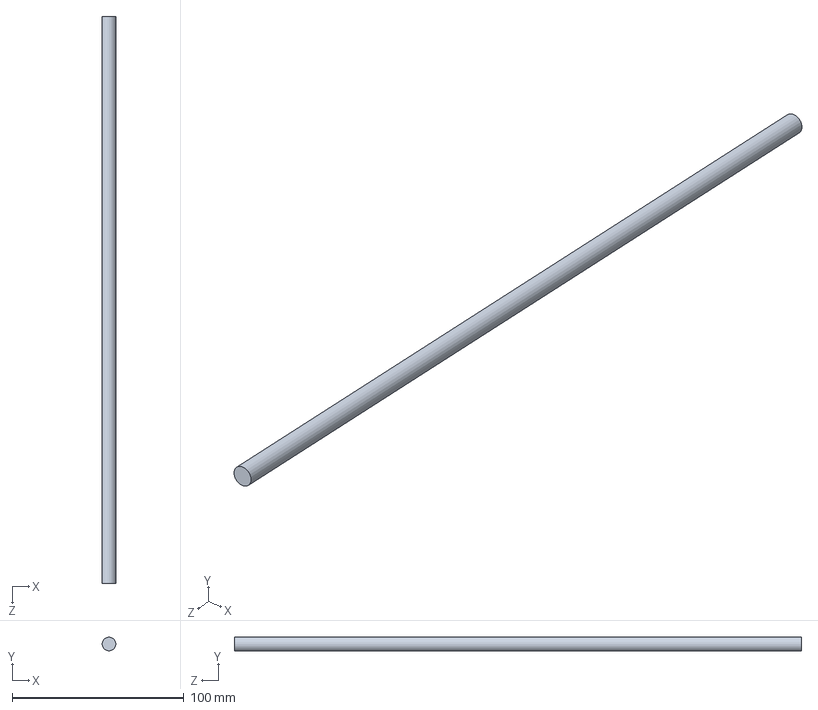
[picture p137: CAD file, 2013-07-26]
MORGAN/MLC-1-0022.SLDPRT
8.00 x 8.00 x 330.0 mm
