angrychisel/makelab-chs-MCAPP/MORGAN/Morgan-master/stl/Eckstruder_Block_for_Prusa.stl

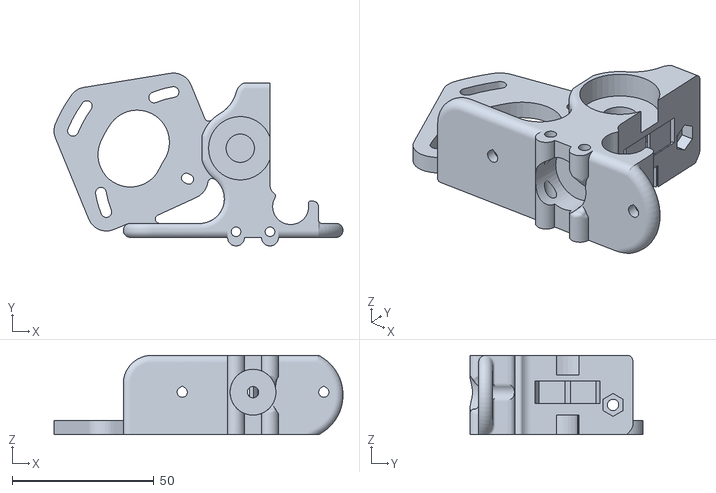
[picture p138: CAD file, 2013-07-25]
MORGAN/Morgan-master/stl/Eckstruder_Block_for_Prusa.stl
102.1 x 61.0 x 28.0
