angrychisel/makelab-chs-MCAPP/MORGAN/pulley 20t gt2 2mm.sldprt

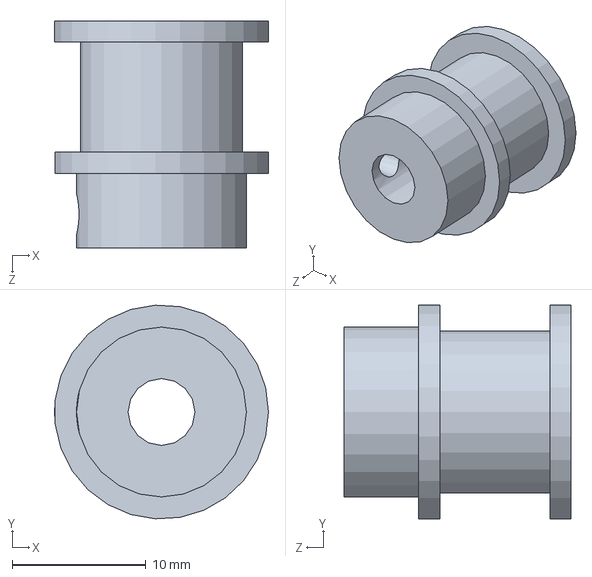
[picture p139: CAD file, 2013-07-26]
MORGAN/pulley 20t gt2 2mm.sldprt
16.0 x 16.0 x 17.0 mm
