angrychisel/makelab-chs-MCAPP/MORGAN/MLC-1-004.SLDPRT

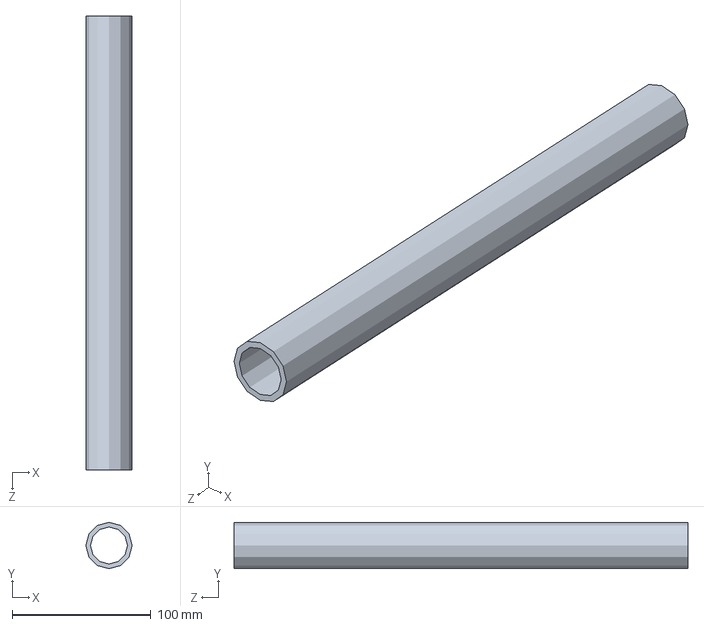
[picture p140: CAD file, 2013-07-26]
MORGAN/MLC-1-004.SLDPRT
33.4 x 33.4 x 327.0 mm
