angrychisel/makelab-chs-MCAPP/MORGAN/MLC-1-0012.SLDPRT

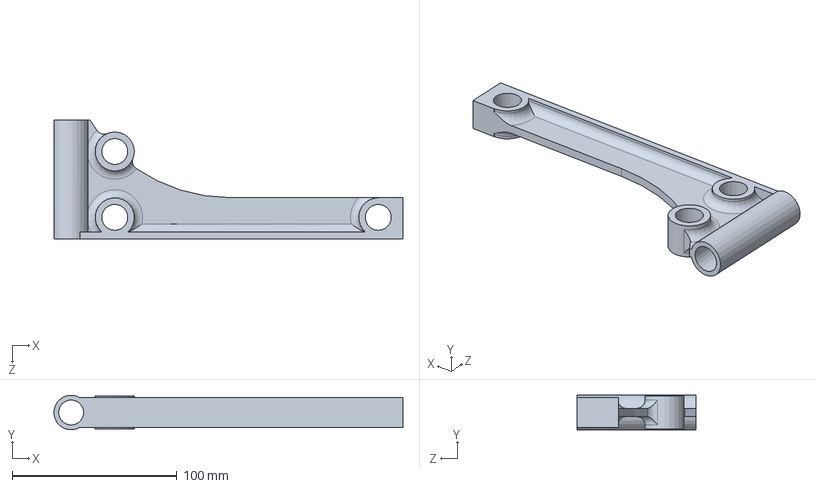
[picture p141: CAD file, 2013-07-25]
MORGAN/MLC-1-0012.SLDPRT
211.9 x 21.0 x 72.0 mm
