angrychisel/makelab-chs-MCAPP/MORGAN/MLC-1-0014.SLDPRT

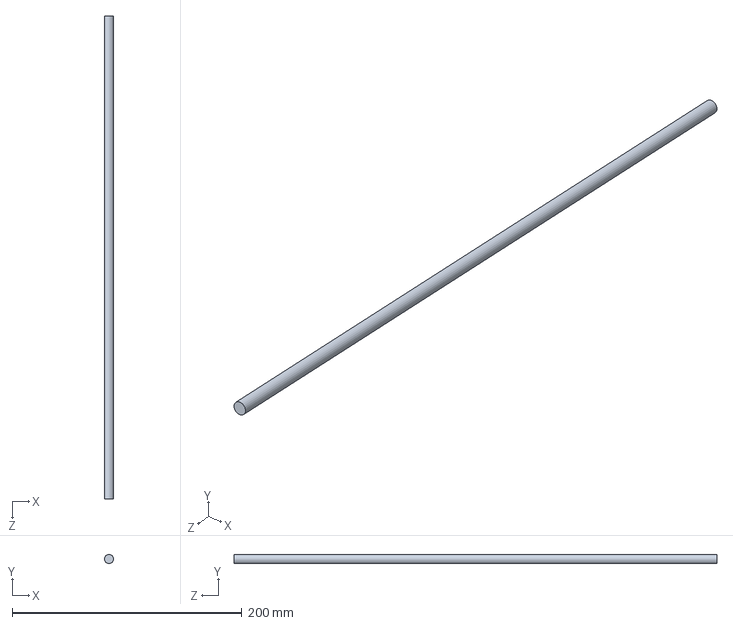
[picture p142: CAD file, 2013-07-25]
MORGAN/MLC-1-0014.SLDPRT
8.00 x 8.00 x 420.0 mm
