angrychisel/makelab-chs-MCAPP/MORGAN/LM8UU.SLDPRT

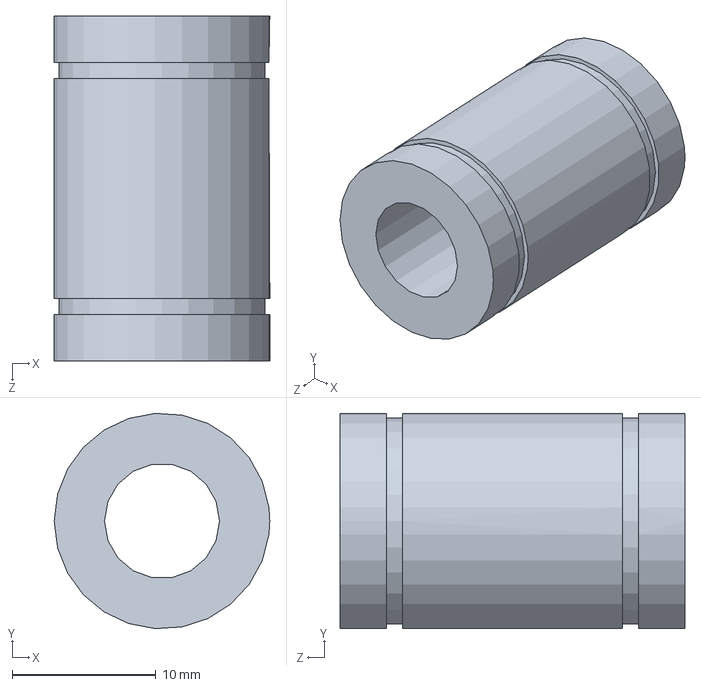
[picture p143: CAD file, 2013-07-25]
MORGAN/LM8UU.SLDPRT
15.0 x 15.0 x 24.0 mm
