angrychisel/makelab-chs-MCAPP/MORGAN/MLC-1-0015.SLDPRT

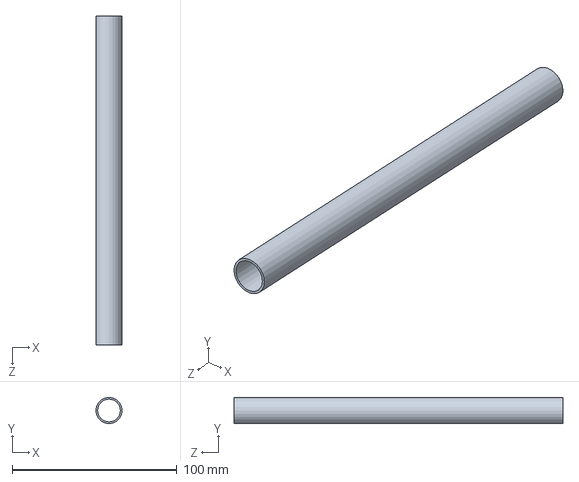
[picture p144: CAD file, 2013-07-25]
MORGAN/MLC-1-0015.SLDPRT
15.9 x 15.9 x 200.0 mm
