angrychisel/makelab-chs-MCAPP/MORGAN/MLC-1-0013.SLDPRT

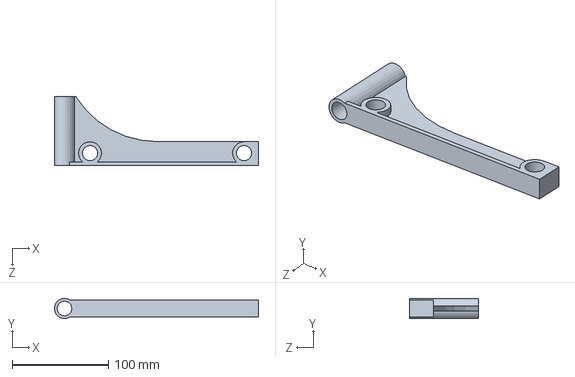
[picture p145: CAD file, 2013-07-25]
MORGAN/MLC-1-0013.SLDPRT
211.9 x 21.0 x 72.0 mm
