angrychisel/makelab-chs-MCAPP/MORGAN/MLC-1-003.SLDPRT

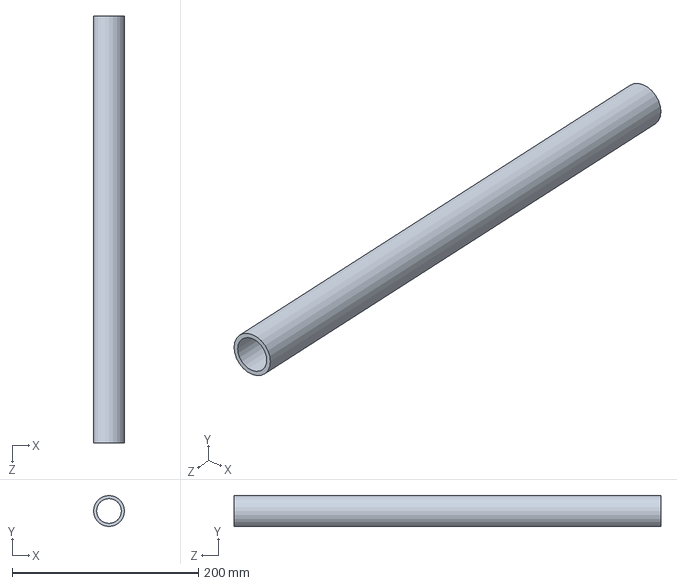
[picture p146: CAD file, 2013-07-25]
MORGAN/MLC-1-003.SLDPRT
33.4 x 33.4 x 459.0 mm
