angrychisel/makelab-chs-MCAPP/MORGAN/FAB APPROVED STL/MLC-1-0021.PDF

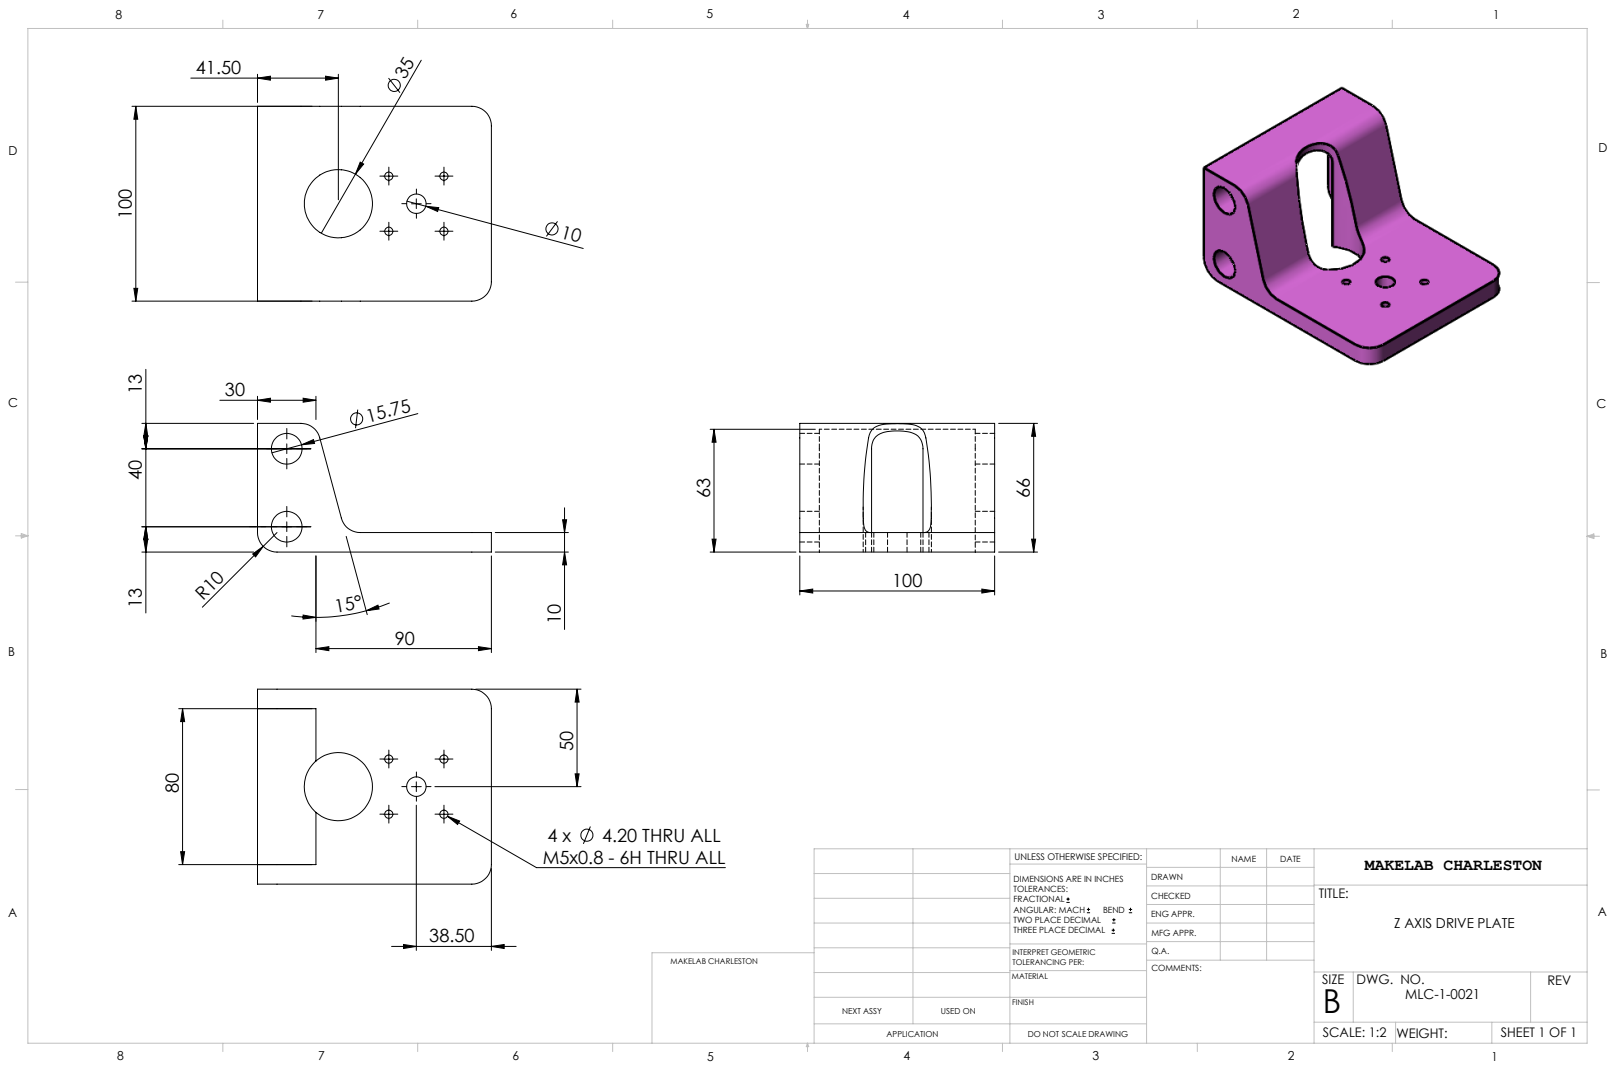
[picture p154: page 1]
4.20 THRU ALL; M5x0.8 - 6H THRU ALL; MAKELAB CHARLESTON; NEXT ASSY; USED ON; ANGULAR: MACH; BEND; INTERPRET GEOMETRIC TOLERANCING PER:; ENG APPR.; MFG APPR.; NAME; DATE; DWG. NO.; REV; SCALE: 1:2 WEIGHT:; SHEET 1 OF 1

UNLESS OTHERWISE SPECIFIED:

DIMENSIONS ARE IN INCHES
TOLERANCES:
FRACTIONAL
TWO PLACE DECIMAL
THREE PLACE DECIMAL

Z AXIS DRIVE PLATE

DO NOT SCALE DRAWING
