angrychisel/makelab-chs-MCAPP/MORGAN/FAB APPROVED STL/MLC-1-006.PDF

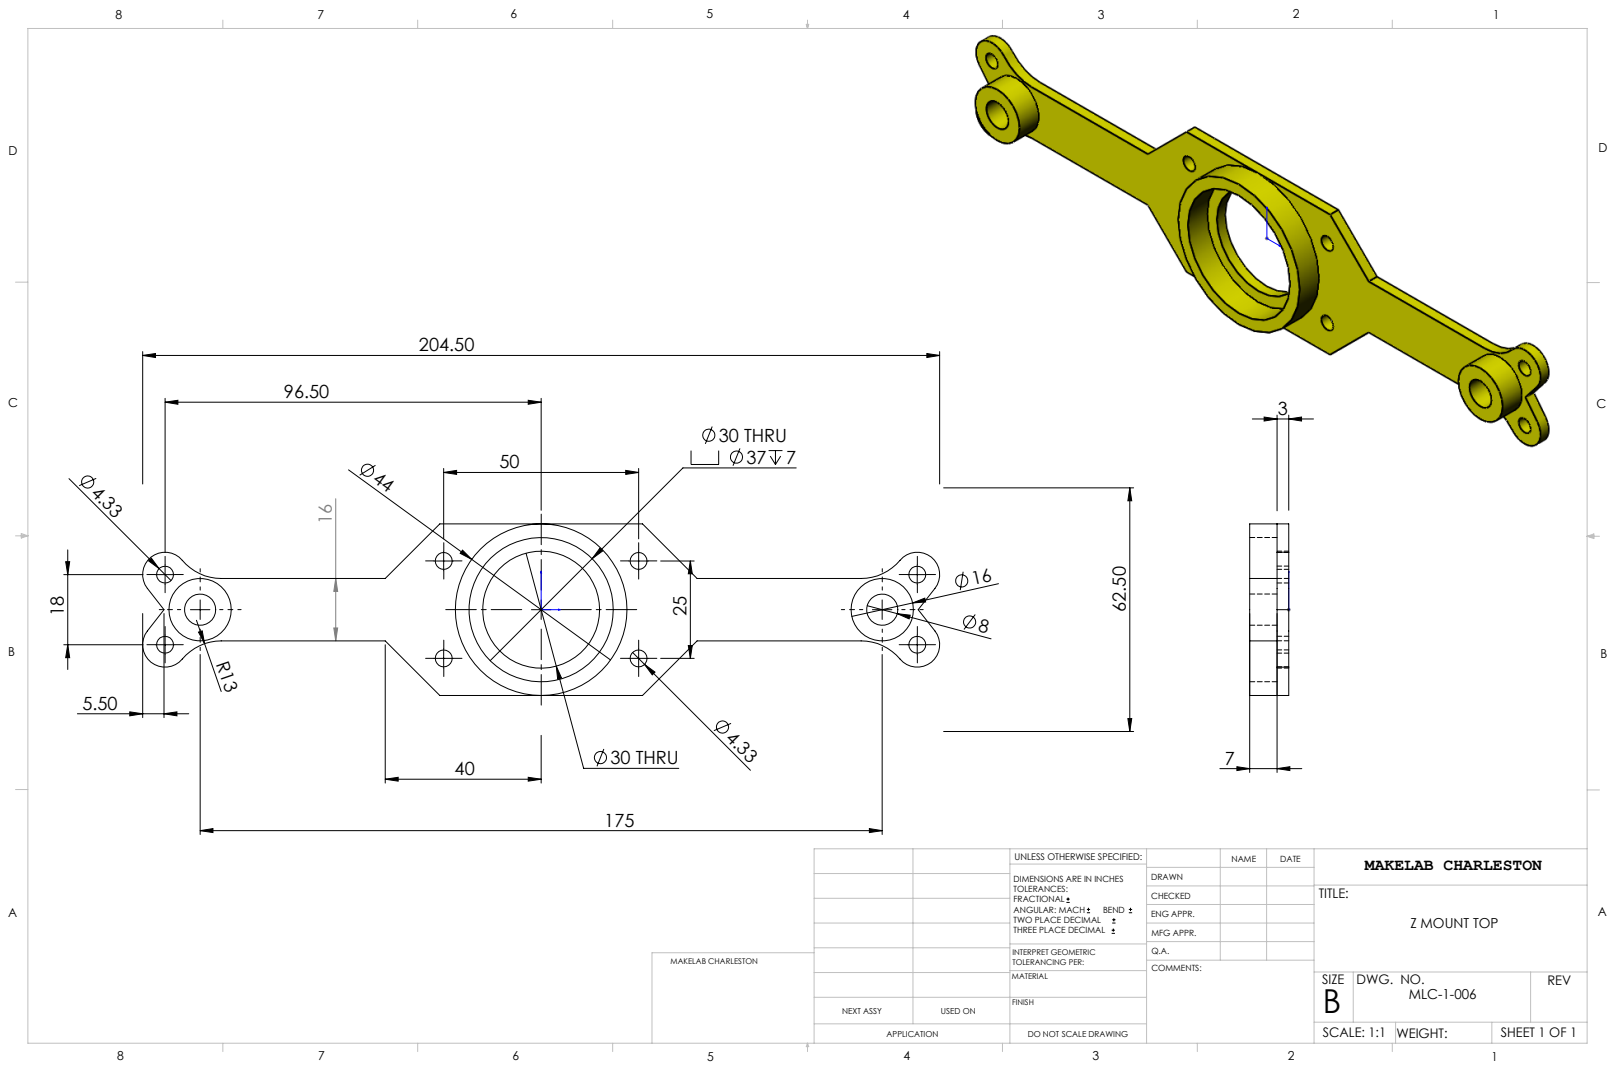
[picture p155: page 1]
30 THRU; 30 THRU 37 7; MAKELAB CHARLESTON; NEXT ASSY; USED ON; ANGULAR: MACH; BEND; INTERPRET GEOMETRIC TOLERANCING PER:; ENG APPR.; MFG APPR.; NAME; DATE; DWG. NO.; REV; SCALE: 1:1 WEIGHT:; Z MOUNT TOP; SHEET 1 OF 1

UNLESS OTHERWISE SPECIFIED:

DIMENSIONS ARE IN INCHES
TOLERANCES:
FRACTIONAL
TWO PLACE DECIMAL
THREE PLACE DECIMAL

DO NOT SCALE DRAWING
